simi1505/20m-SSB-TRX-Prototype-OE3SDE/Transmitter/Calculations/Buffer Amplifier/Buffer Amplifier.pdf

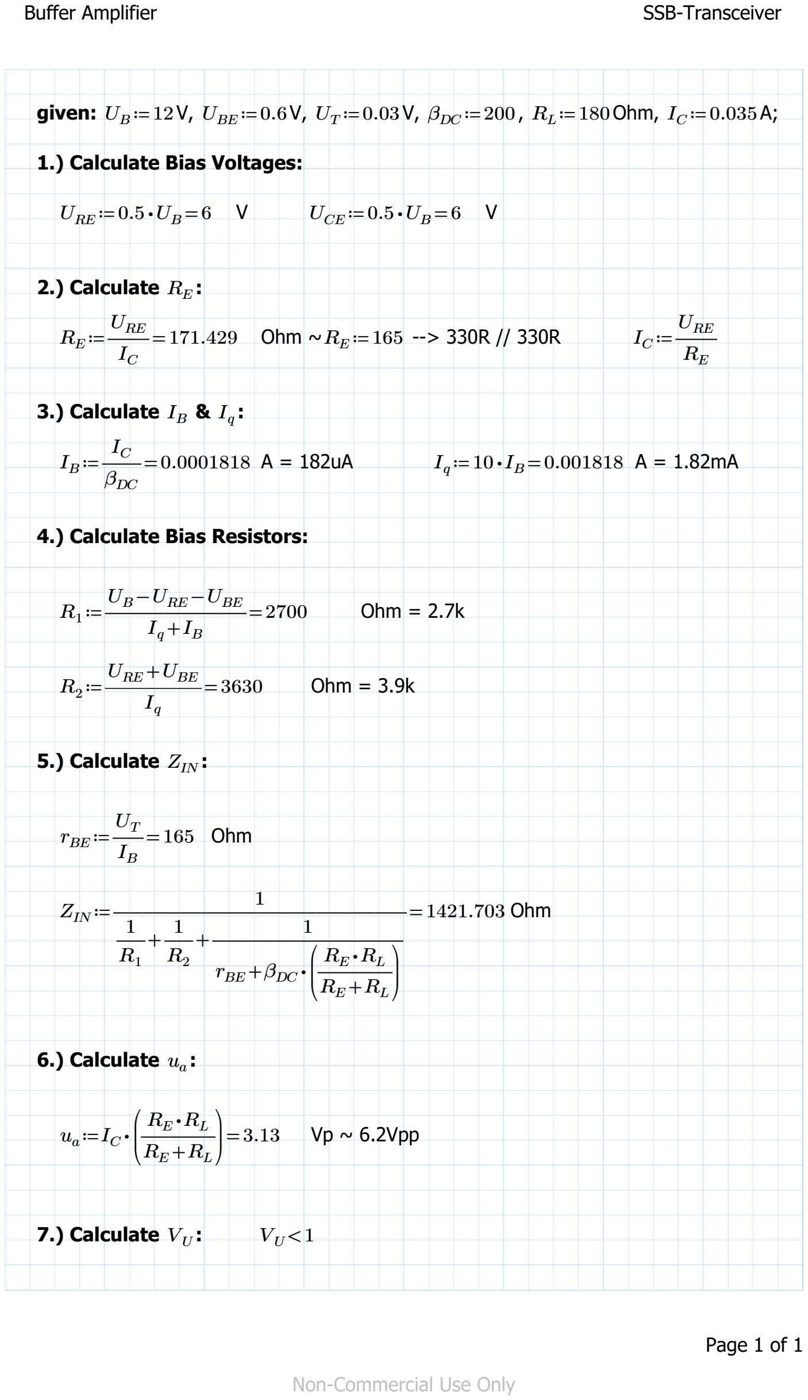
[picture p11: page 1]

Buffer Amplifier | SSB-Transceiver
given: UB≔12V, UBE≔0.6V, UT≔0.03V, βDC≔200 , R ≔ | Ohm, | A; L | 180 | IC≔0.035

1.) Calculate Bias Voltages:

URE≔0.5 ⋅UB =6 V UCE≔0.5 ⋅UB =6 V

2.) Calculate RE :

RE≔――=

URE
IC
171.429 Ohm ~RE≔165 --> 330R // 330R | IC≔――

URE
RE

3.) Calculate IB & I : q

IB≔――=

IC

βDC

0.0001818 A = 182uA | Iq≔10 ⋅ IB =0.001818 A = 1.82mA

4.) Calculate Bias Resistors:

R1≔―――――=

UB −URE −UBE
Iq+IB

2700 Ohm = 2.7k

R2≔――――=

URE +UBE
Iq

3630 Ohm = 3.9k

5.) Calculate Z : IN

rBE≔――=

UT
IB

165 Ohm

ZIN≔―――――――――――=

1

―+ +

1
R1

―1
R2

――――1 ―――

rBE +βDC ⋅

⎛
⎜
⎝

―――

RE ⋅RL
RE +RL

⎞
⎟
⎠

1421.703 Ohm

6.) Calculate u : a

ua≔IC ⋅ | =

⎛
⎜
⎝
| ―――

RE ⋅RL
RE +RL

⎞
⎟
⎠

### 3.13 Vp ~ 6.2Vpp

7.) Calculate VU : VU <1

Non-Commercial Use Only

Page 1 of 1
