simi1505/20m-SSB-TRX-Prototype-OE3SDE/Transmitter/Calculations/Driver Amplifier/Driver Amplifier.pdf

Driver Amplifier | SSB-Transceiver

geg.: UB≔12V, PO2≔1.2W, η≔0.3 , UT≔0.026V, f≔14000000Hz,
RL≔50Ohm

1.) Calculate Stage 2:

a) Calculate Voltages:

URE2≔0.1 ⋅UB =1.2V

UBE2≔0.7 V

b) Calculate bias currents: | βDC2≔180
IC2≔――⋅ | =

PO2
η ―1 ―UB
0.333 A

IB2≔――=

IC2

βDC2

0.001852 A

IQ2≔5 ⋅ IB2=0.009259 A

c) Calculate resistors:

RC2≔―――――=

⎛⎝UB −URE2⎞
⎠

2

2 ⋅PO2

### 48.6 Ohm

RE2≔――=

URE2

IC2

3.6 Ohm | RE2≔3.3 Ohm

R12≔――――――=

UB −UBE2−URE2

IB2+IQ2

909 | Ohm | R12≔1000 Ohm

R22≔――――=

UBE2+URE2

IQ2

205.2 | Ohm | R22≔220 Ohm

Non-Commercial Use Only

Page 1 of 4

d) Calculate gain resistor: | GdB2≔12 = 15.85

RE2'≔―――=

RC2

10

――

GdB2
10

3.066 Ohm

REx2≔――――=

1

――−

1

RE2'

―1―RE2

43.329 REx2≔43 Ohm

e) Calculate input resistance: | fT2≔200000000 Hz

βAC2≔――=

fT2
f

14.286 re2≔――=

UT

IC2

0.078 Ohm

RIN2≔――――――――――=

1

――+ +

1

R12

―1 ―R22

―――1 ――― βAC2 ⋅ ⎛⎝re2+RE2'⎞ ⎠

35.962 Ohm

2.) Calculate Stage 1:

a) Calculate Voltages:

URE1≔0.1 ⋅UB =1.2V

UBE1≔0.7 V

b) Calculate bias currents: | βDC1≔210

PO1≔―――=

PO2

10

――

GdB2
10

0.076 W

IC1≔――⋅ =

PO1
η ―1 ―UB
0.021 A

IB1≔――=

IC1 βDC1 | 0.0001 A

IQ1≔6 ⋅ IB1=0.000601 A

Page 2 of 4

c) Calculate resistors:

RC1≔―――――=

⎛⎝UB −URE1⎞
⎠

2

2 ⋅PO1

770.258 Ohm

RE1≔――=

URE1

IC1

57.056 Ohm | RE1≔56 Ohm

R11≔――――――=

UB −UBE1−URE1

IB1+IQ1

14406.679 Ohm R11≔15000 Ohm

R21≔――――=

UBE1+URE1

IQ1

3161.862 Ohm | R21≔3300 Ohm
d) Calculate gain resistor: | GdB1≔20 = 100

RE1'≔―――=

RC1

10

――

GdB1
10

7.703 Ohm

REx1≔――――=

1

――−

1

RE1'

―1―RE1

8.931 REx1≔8.5 Ohm

e) Calculate input resistance: | fT1≔300000000 Hz

βAC1≔――=

fT1
f

21.429 re1≔――=

UT

IC1

1.236 Ohm

RIN1≔――――――――――=

1

――+ +

1

R11

―1 ―R21

―――1 ――― βAC1 ⋅ ⎛⎝re1+RE1'⎞ ⎠

178.879 Ohm

Page 3 of 4

3.) Calculate Transformer:

a) Stage 1 output transformer:
ZP≔RC1=770.258 | Ohm | ZS≔RIN2=35.962 Ohm
| | --> Guideline: 6T:28T @ FT37-43 Toroid Core --> LP≔113.4 ⋅ 10 H @ FT37-43 Toroid Core ⁻⁶ --> LS≔5.6 ⋅ 10 H @ FT37-43 Toroid Core ⁻⁶
ü1≔ | =
―
ZP ZS | 4.628

üdB1≔10 ⋅log⎛⎝ü1

| ⎞ ⎠=6.654 dB --> 6.654dB loss!

ZP≔ZS

⋅ =

⎛
⎜

⎝―18
4

⎞
⎟
⎠

2
728.237 Ohm

Requirement:

XLP≔2 ⋅π⋅ f ⋅LP=9975.185 | Ohm > 10 ⋅RC1=7702.581 Ohm --> correct!
XLS≔2 ⋅π⋅ f ⋅LS=492.602 | Ohm > 10 ⋅R = | Ohm --> correct! IN2 359.623
b) Stage 2 output transformer:
ZP≔RC2=48.6 | Ohm | ZS≔RL=50 | Ohm

--> Guideline: 6T:28T @ FT37-43 Toroid Core
| | --> LP≔8.75 ⋅ 10 H @ FT37-43 Toroid Core ⁻⁶ --> LS≔8.75 ⋅ 10 H @ FT37-43 Toroid Core ⁻⁶
ü2≔ | =
―
ZP ZS | 0.986

üdB2≔10 ⋅log⎛⎝ü2

⎞
⎠=−0.062 dB --> 0.062dB gain!

ZP≔ZS

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
### 50 Ohm

Requirement:

XLP≔2 ⋅π⋅ f ⋅LP=769.69 | Ohm > 10 ⋅RC2=486 Ohm --> correct!
XLS≔2 ⋅π⋅ f ⋅LS=769.69 | Ohm > 10 ⋅R = | Ohm --> correct! L 500

4.) Gain of Driver Amplifier:

Gges≔GdB1−üdB1+GdB2−üdB2=25.408

Page 4 of 4
