simi1505/20m-SSB-TRX-Prototype-OE3SDE/Transmitter/Calculations/LC Double Tuned Bandpass Filter/LC Double Tuned Bandpass Filter.pdf

LC Double Tuned Bandpass Filters | SSB-Transceiver

Circuit:


1.) Define lower and upper cut off frequencies:

f1≔14000000 f2≔14400000

2.) Define inductor core, turns and value (L＝L ＝ ): 1 | L2
L≔2.12 ⋅ 10⁻⁶ | H = 2.12uH --> 23T @ T50-6 Core --> "toroids.info/T50-6.php"
QU≔240 | ... unloaded Q of the resonators

3.) Calculate ω : 0

ω0

... center angular frequency

ω0≔2 ⋅π⋅ f1

⋅f2

=89212381.366 rad/sec

4.) Calculate C : 0

C0

... nodal capacitance

C0≔―――=

1
ω ⋅ 0

### 2 L

0.0000000000593 F = 59.3pF

5.) Calculate Q : L

QL

... loaded filter Q

QL≔―――――=

ω0
2 ⋅π⋅ ⎛⎝f2−f1

⎞
⎠

35.496

Non-Commercial Use Only

Page 1 of 3

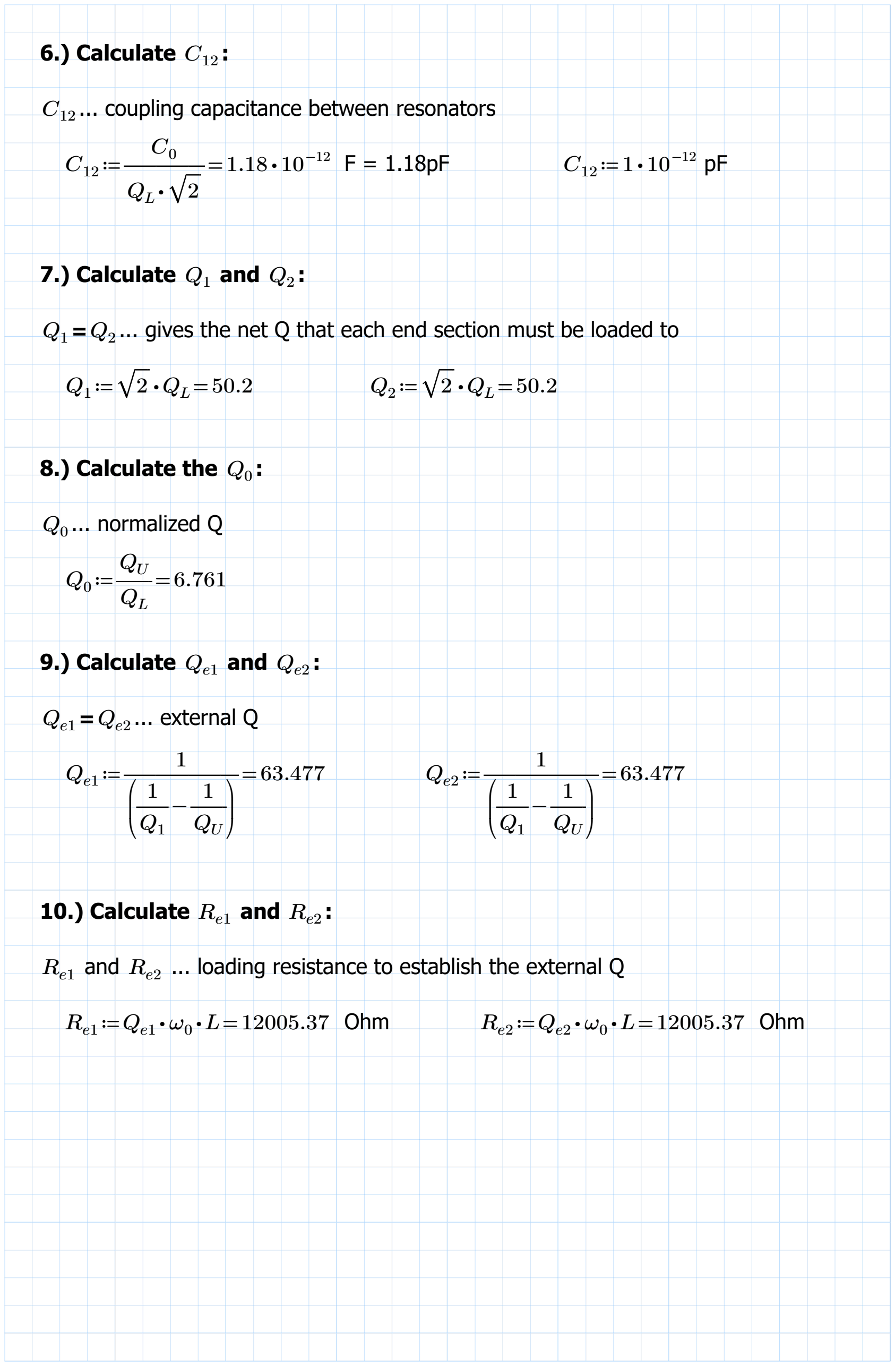
[picture p12: figure]
6.) Calculate C : 12; 7.) Calculate Q and; 8.) Calculate the Q : 0; ... normalized Q; 9.) Calculate Q and; Qe1＝Qe2 ... external Q; 10.) Calculate R and; ⋅L=12005.37 Ohm

C ... coupling capacitance between resonators 12

1.18 ⋅ 10⁻¹² F = 1.18pF | C12≔1 ⋅ 10⁻¹² pF

... gives the net Q that each end section must be loaded to

Re1 and Re2 ... loading resistance to establish the external Q

Page 2 of 3

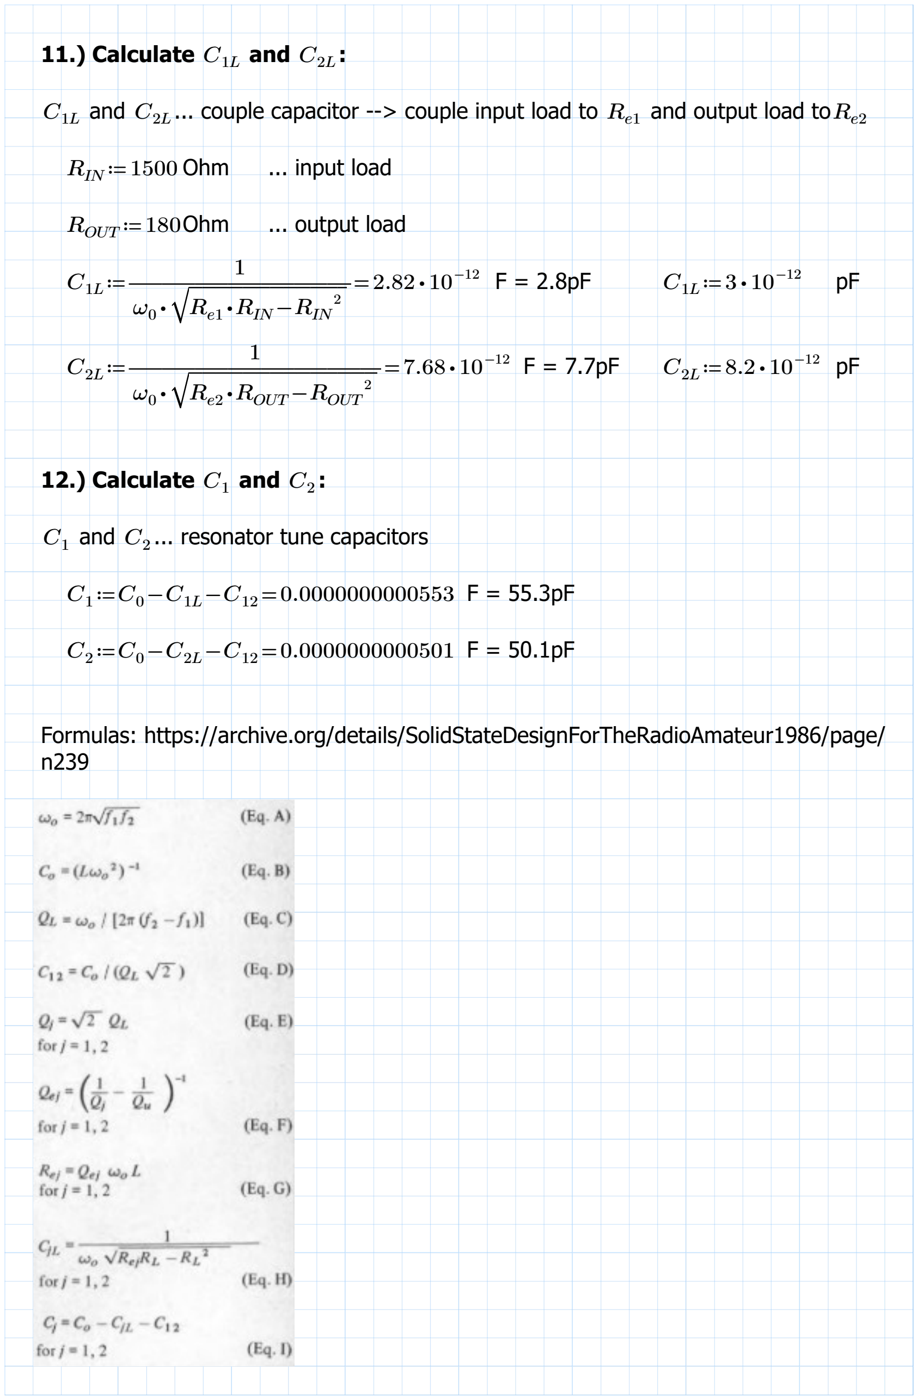
[picture p13: figure]
11.) Calculate C and; RIN≔1500 Ohm; ... input load; ROUT≔180Ohm; ... output load; − R ⋅ e1 RIN RIN; − R ⋅ e2 ROUT ROUT; 12.) Calculate C and; C and; ... resonator tune capacitors 1; Formulas: https://archive.org/details/SolidStateDesignForTheRadioAmateur1986/page/ n239

C1L and C2L ... couple capacitor --> couple input load to Re1 and output load toRe2

7.68 ⋅ 10⁻¹² F = 7.7pF C2L≔8.2 ⋅ 10⁻¹² pF

Page 3 of 3
