simi1505/20m-SSB-TRX-Prototype-OE3SDE/Transmitter/Calculations/LC Lowpass Filter/LC Lowpass Filter.pdf

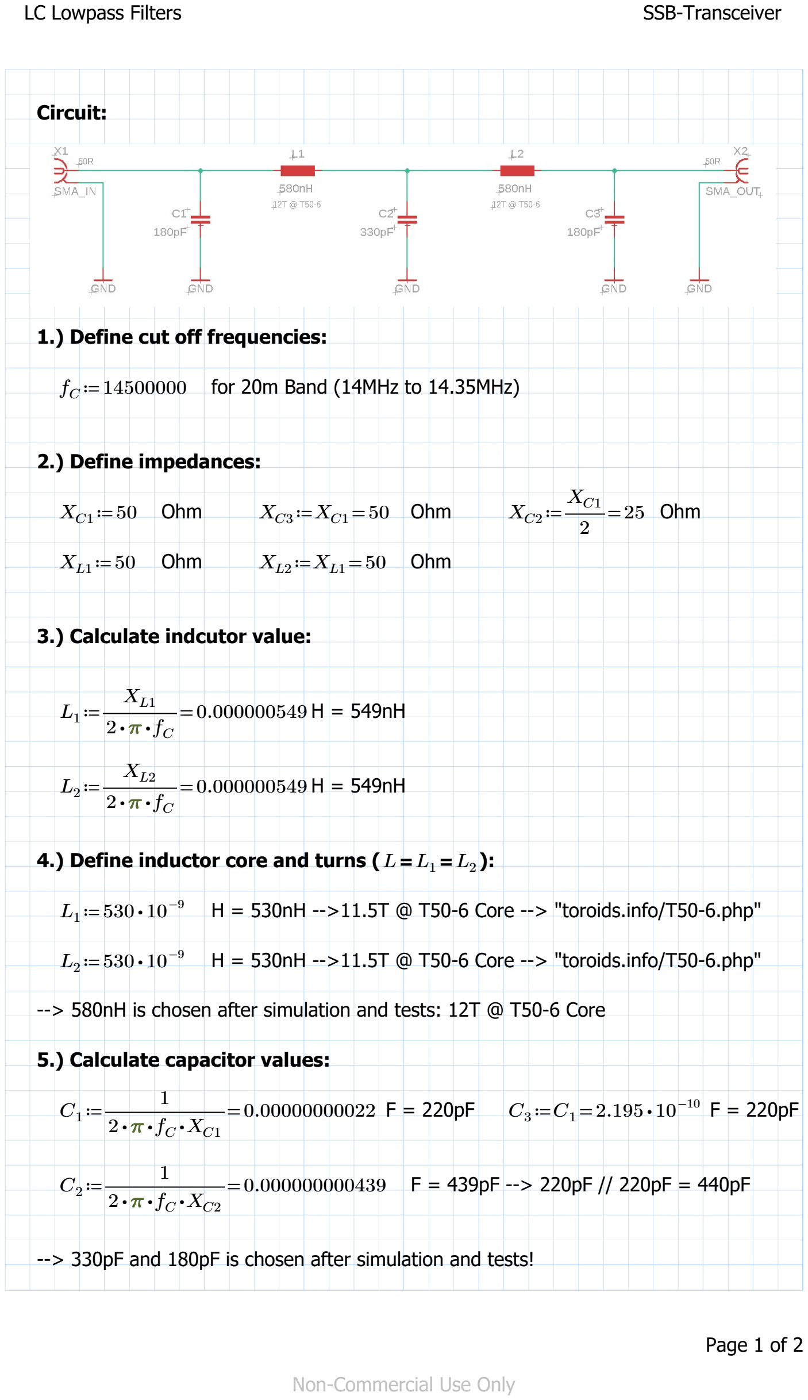
[picture p14: page 1]

LC Lowpass Filters | SSB-Transceiver

Circuit:

1.) Define cut off frequencies:

fC≔14500000 for 20m Band (14MHz to 14.35MHz)

2.) Define impedances:
XC1≔50 Ohm | XC3≔XC1=50 Ohm | XC2≔――= XC1
| | 2

### 25 Ohm

XL1≔50 Ohm XL2≔XL1=50 Ohm

3.) Calculate indcutor value:

L1≔―――=

XL1
2 ⋅π⋅ fC

0.000000549 H = 549nH

L2≔―――=

XL2
2 ⋅π⋅ fC

0.000000549 H = 549nH

4.) Define inductor core and turns (L＝L ＝ ): 1 L2

L1≔530 ⋅ 10⁻⁹ H = 530nH -->11.5T @ T50-6 Core --> "toroids.info/T50-6.php"

L2≔530 ⋅ 10⁻⁹ H = 530nH -->11.5T @ T50-6 Core --> "toroids.info/T50-6.php"

--> 580nH is chosen after simulation and tests: 12T @ T50-6 Core

5.) Calculate capacitor values:

C1≔―――――=

1 2 ⋅π⋅ fC ⋅XC1 | 0.00000000022 F = 220pF | C3≔C1=2.195 ⋅ 10⁻¹⁰ F = 220pF

C2≔―――――=

1
2 ⋅π⋅ fC ⋅XC2

0.000000000439 F = 439pF --> 220pF // 220pF = 440pF

--> 330pF and 180pF is chosen after simulation and tests!

Non-Commercial Use Only

Page 1 of 2

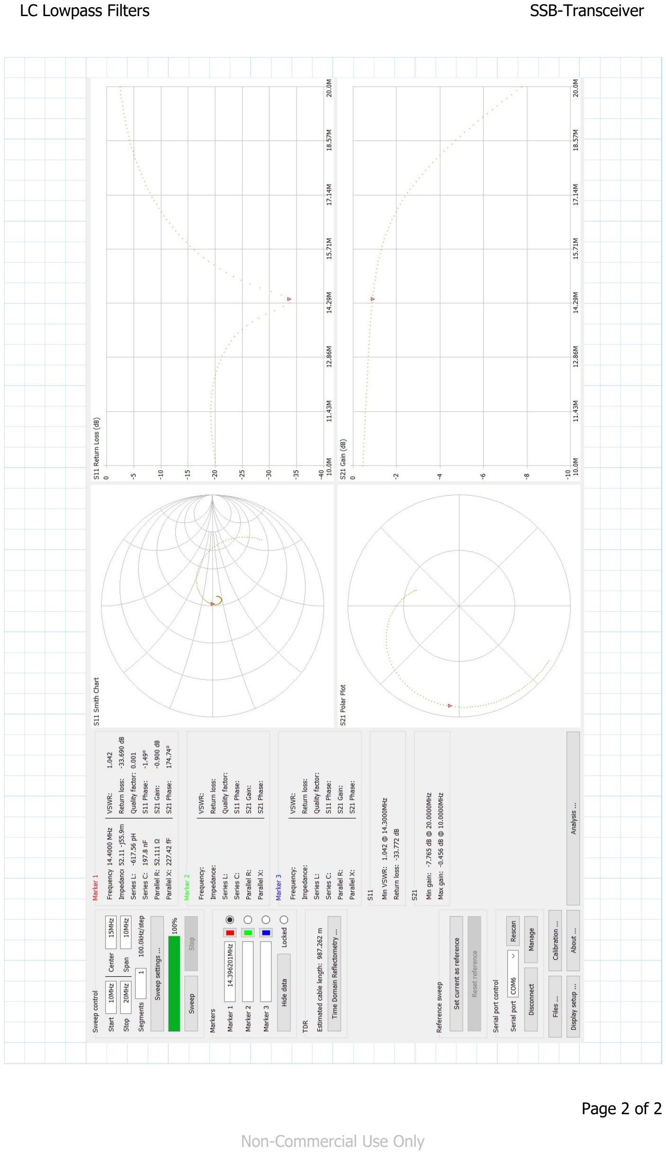
[picture p15: page 2]

LC Lowpass Filters | SSB-Transceiver

Non-Commercial Use Only

Page 2 of 2
