simi1505/20m-SSB-TRX-Prototype-OE3SDE/Transmitter/Calculations/Mic. Amplifier/Mic. Amplifier Gain.pdf

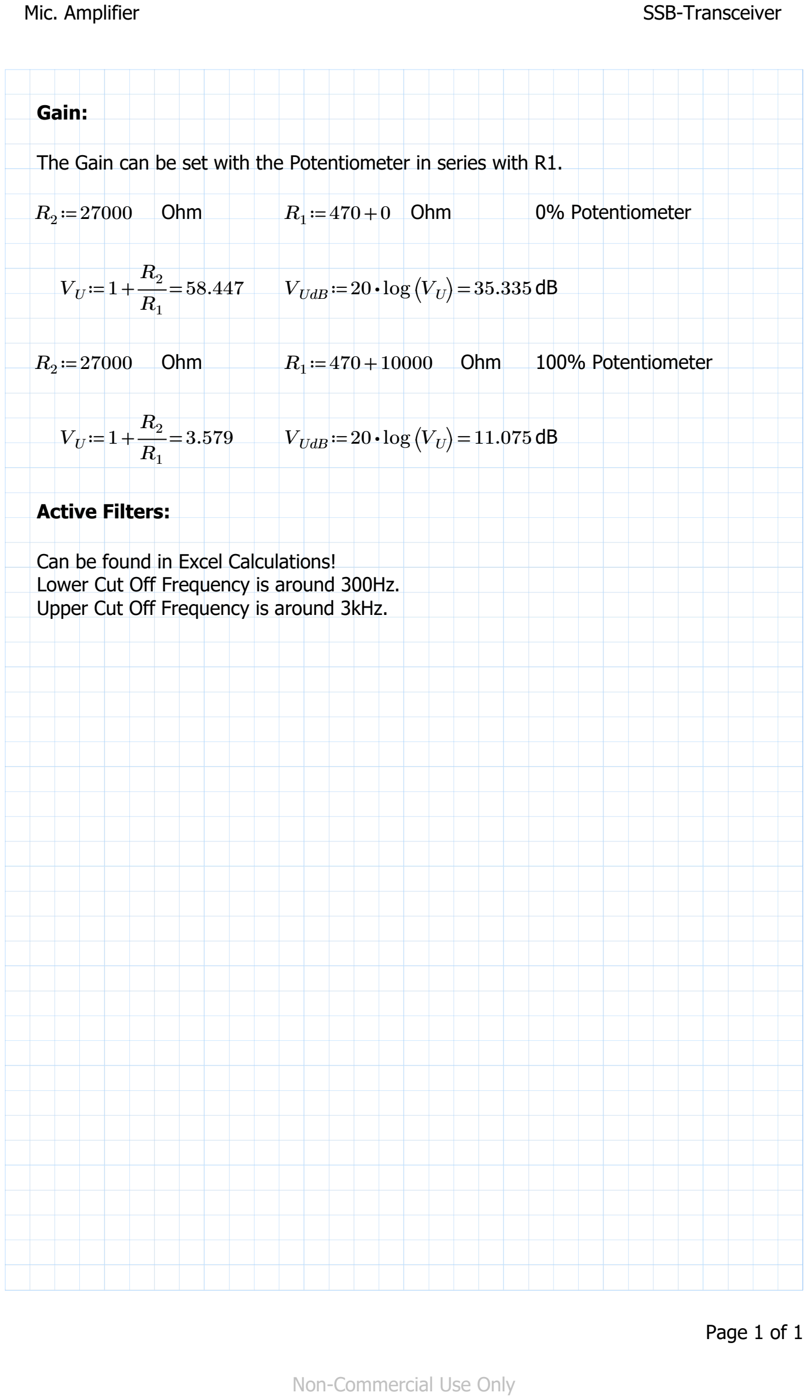
[picture p16: page 1]

Mic. Amplifier | SSB-Transceiver

Gain:

The Gain can be set with the Potentiometer in series with R1.

R2≔27000 | Ohm | R1≔470+0 Ohm | 0% Potentiometer

VU≔1+―=

| R2 R1
58.447 VUdB≔20 ⋅log⎛⎝VU
| | ⎞
⎠=35.335 dB
R2≔27000 | Ohm | R1≔470+10000 Ohm | 100% Potentiometer

VU≔1+―=

| R2 R1
3.579 VUdB≔20 ⋅log⎛⎝VU
| | ⎞
⎠=11.075 dB

Active Filters:

Can be found in Excel Calculations!
Lower Cut Off Frequency is around 300Hz. Upper Cut Off Frequency is around 3kHz.

Non-Commercial Use Only

Page 1 of 1
