simi1505/20m-SSB-TRX-Prototype-OE3SDE/Transmitter/Calculations/Power Amplifier/Power Amplifier.pdf

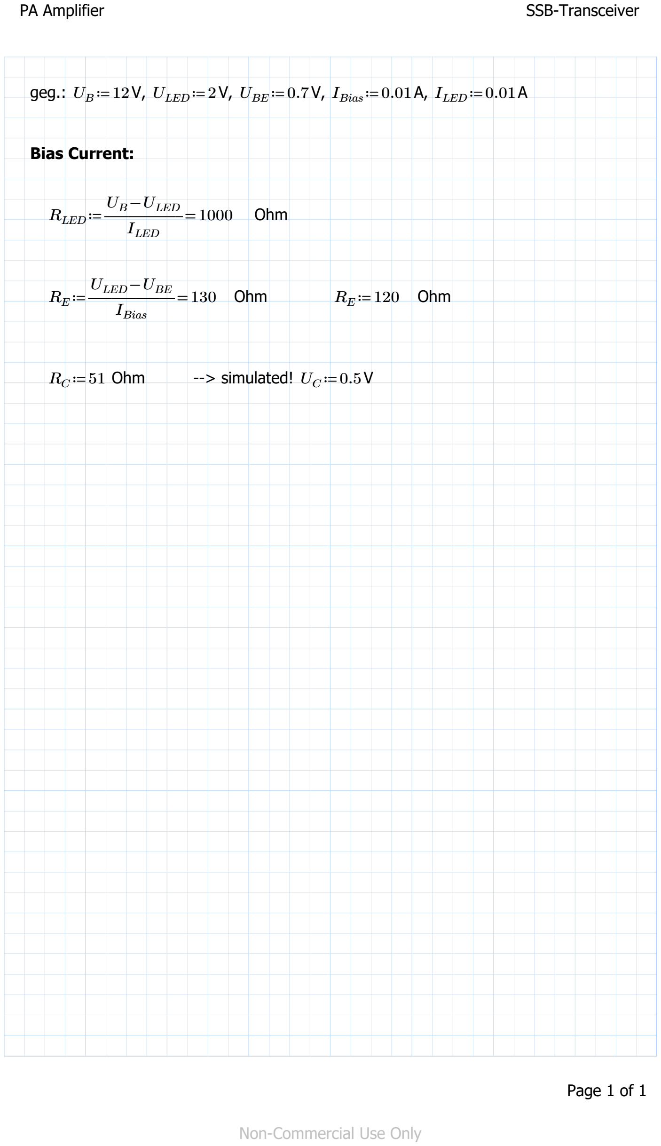
[picture p17: page 1]

PA Amplifier | SSB-Transceiver

geg.: UB≔12V, ULED≔2V, UBE≔0.7V, IBias≔0.01A, ILED≔0.01A

Bias Current:

RLED≔――――=

UB −ULED

ILED

1000 Ohm

RE≔――――=

ULED −UBE

IBias

130 Ohm | RE≔120 Ohm
RC≔51 Ohm | --> simulated! UC≔0.5V

Non-Commercial Use Only

Page 1 of 1
