simi1505/20m-SSB-TRX-Prototype-OE3SDE/Receiver/Eagle Files/LC Double Tuned Bandpass Filters/SSB Transceiver_LC Double Tuned Bandpass Filter_Circuit.pdf

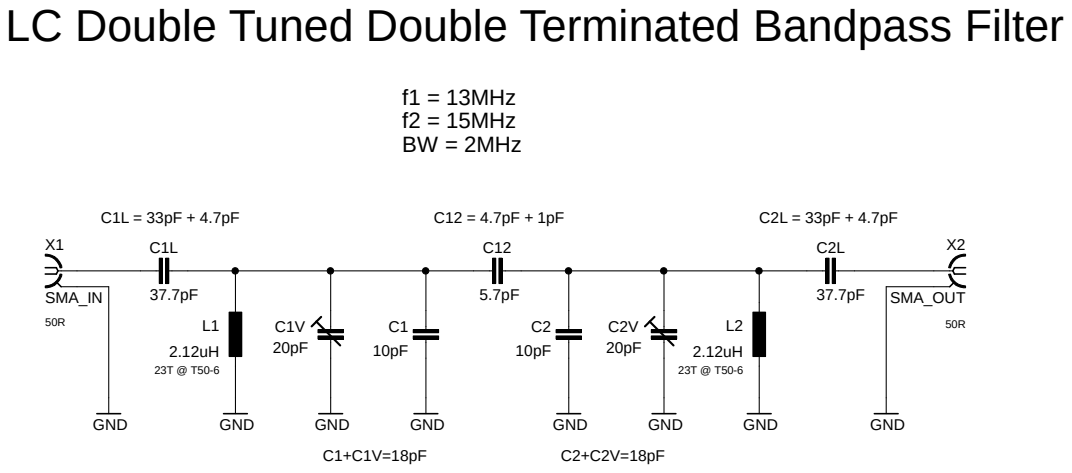
[picture p25: page 1]

11/02/2020 19:53 E:\Simon Dorrer\DIY Projekte\Amateurfunkprojekte\SSB Transceiver\Receiver\Eagle Files\LC Double Tuned Bandpass Filters\SSB Transceiver_LC Double Tuned Bandpass Filter.sch (Sheet: 1/1) 50R 50R C1+C1V=18pF C2+C2V=18pF 23T @ T50-6 23T @ T50-6 f1 = 13MHz f2 = 15MHz BW = 2MHz LC Double Tuned Double Terminated Bandpass Filter C1L = 33pF + 4.7pF C2L = 33pF + 4.7pF C12 = 4.7pF + 1pF SMA_IN SMA_OUT GND GND 37.7pF 5.7pF 10pF 10pF 37.7pF GND GND GND GND 2.12uH 2.12uH 20pF 20pF GND GND X1 C1L C12 X2 C1 C2 C2L L1 L2 C1V C2V Date: Sheet: REV: TITLE: Document Number: 11/02/2020 19:50 1/1 SSB Transceiver_LC Double Tuned Bandpass Filter
