simi1505/20m-SSB-TRX-Prototype-OE3SDE/Receiver/Eagle Files/MC1496 Product Detector/SSB Transceiver_MC1496 Product Detector_Circuit.pdf

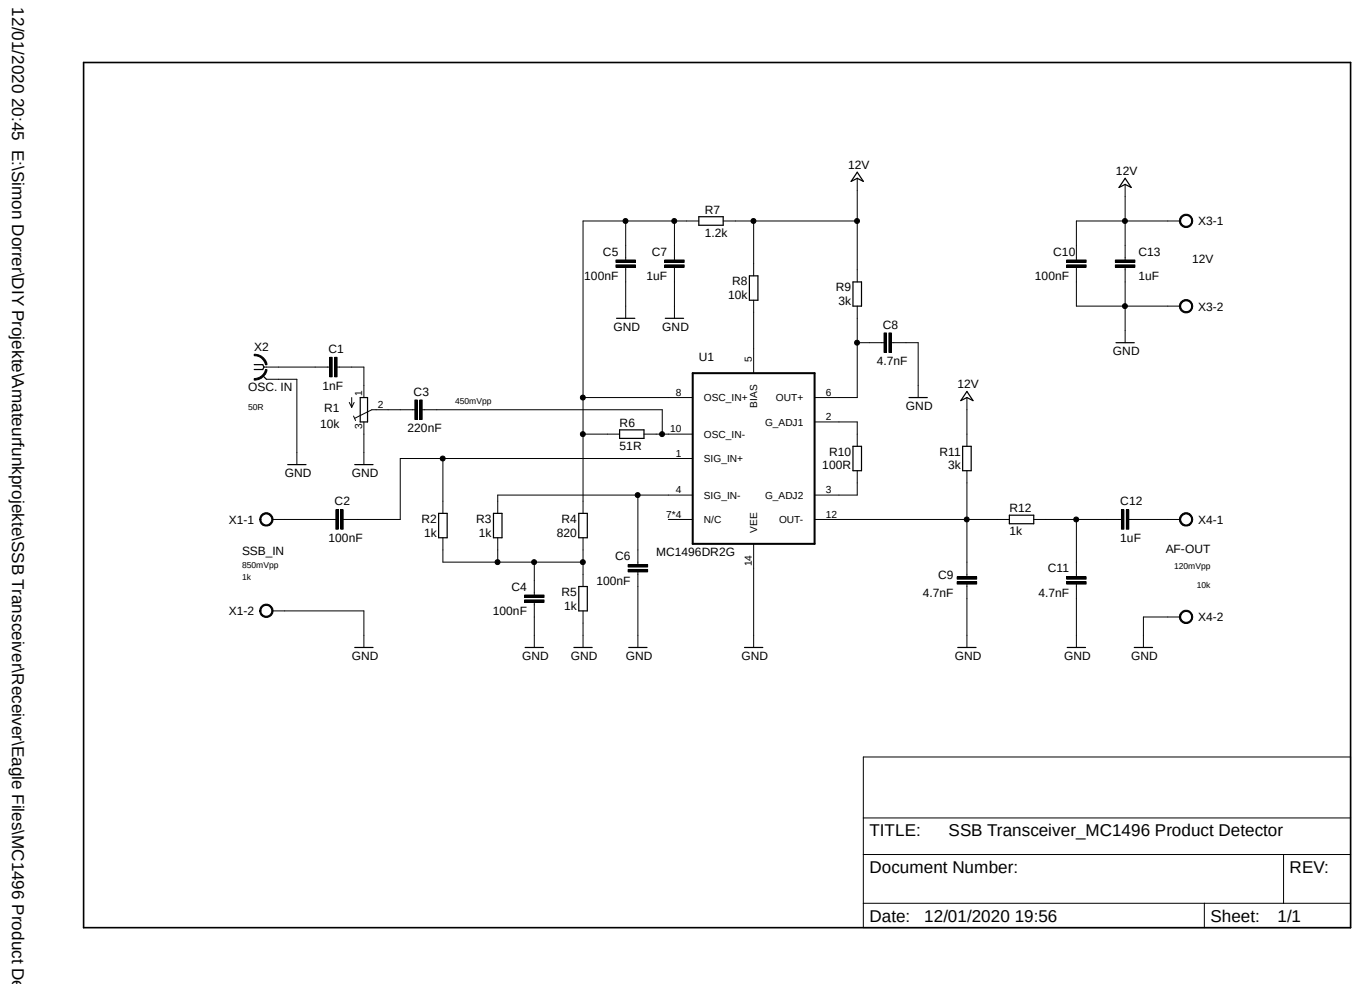
[picture p26: page 1]

12/01/2020 20:45 E:\Simon Dorrer\DIY Projekte\Amateurfunkprojekte\SSB Transceiver\Receiver\Eagle Files\MC1496 Product Detector\SSB Transceiver_MC1496 Product Detector.sch (Sheet: 1/1) 10k 120mVpp 50R 450mVpp 850mVpp 1k GND 12V GND OSC. IN 1nF 10k 220nF GND 51R 1k MC1496DR2G 1uF 100R SSB_INGND 1uF 12V GND 10k 1.2k 100nF 1uF 8201k 1k 100nF GND GND 100nFGND GND GND 100nF 3k 4.7nFGND AF-OUT 4.7nF 4.7nF 1k 3k12V GND GND 12V 100nFGND X3-1 X3-2 X2 C1

14 OUT- 12 U1 C12 R10 X1-1 X1-2 C13 R8 R7 C5 C7 R4 R5 R2 C6 C2 C10 R9 C8 X4-1 X4-2 C11 C9 R12 R11 C4 Date: Sheet: REV: TITLE: Document Number: 12/01/2020 19:56 1/1 SSB Transceiver_MC1496 Product Detector
