simi1505/20m-SSB-TRX-Prototype-OE3SDE/Receiver/Eagle Files/SA612 Mixer/SSB Transceiver_SA612 Mixer_Circuit.pdf

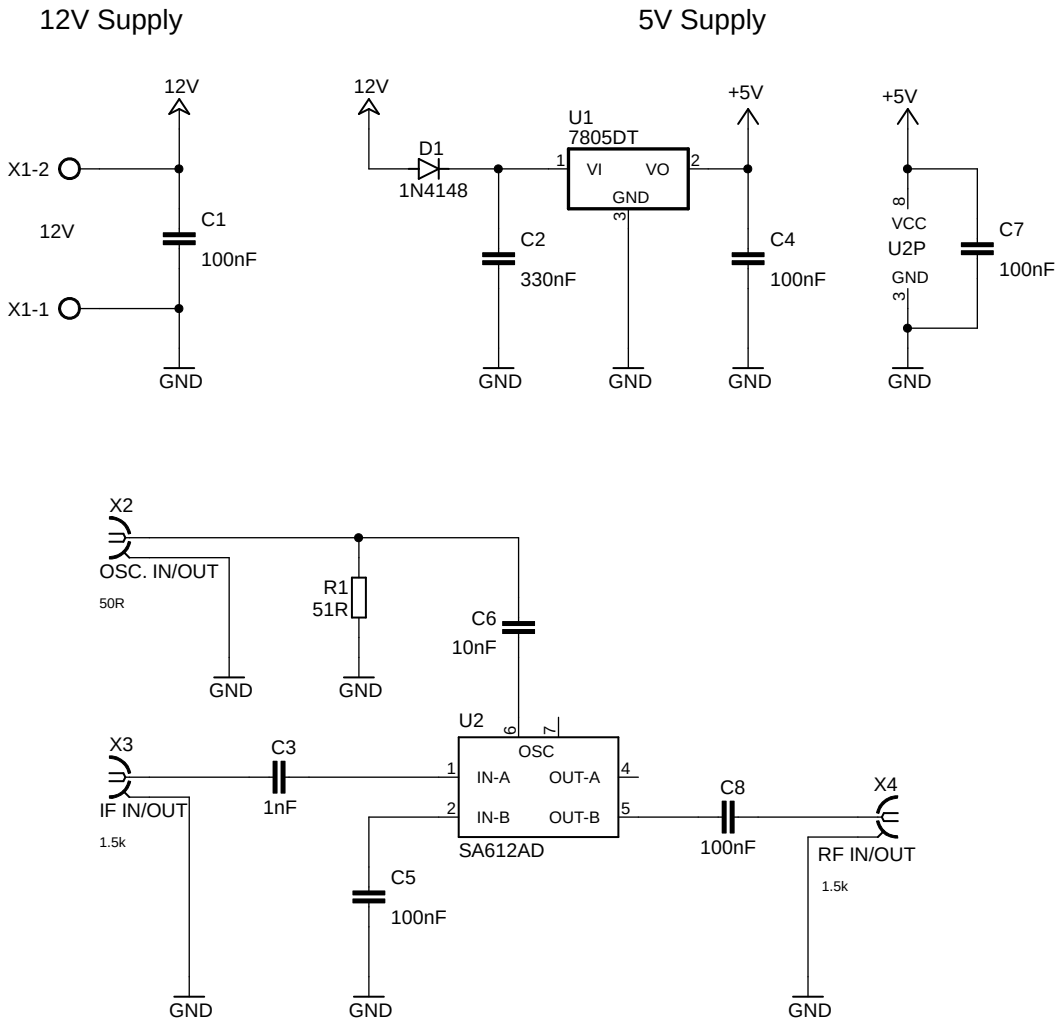
[picture p27: page 1]

12/01/2020 17:15 E:\Simon Dorrer\DIY Projekte\Amateurfunkprojekte\SSB Transceiver\Transmitter\Eagle Files\SA612 Mixer\SSB Transceiver_SA612 Mixer.sch (Sheet: 1/1) 1.5k 50R 1.5k 12V Supply 5V Supply RF IN/OUT GND OSC. IN/OUTGND 100nF 12V GND IF IN/OUT 12V +5V 7805DT 330nF 100nF 1N4148SA612AD 100nF GND 1nF 10nF 100nF GND GND GND GND GND +5V 100nF 12V 51RGND X4 X2 C1 X3 X1-1 X1-2 GND VI 1

8 3 U2P C5 C3 C6 C8 C7 R1 Date: Sheet: REV: TITLE: Document Number: 12/01/2020 17:14 1/1 SSB Transceiver_SA612 Mixer
