simi1505/20m-SSB-TRX-Prototype-OE3SDE/Receiver/Eagle Files/Speaker Amplifier/SSB Transceiver_Speaker Amplifier_Circuit.pdf

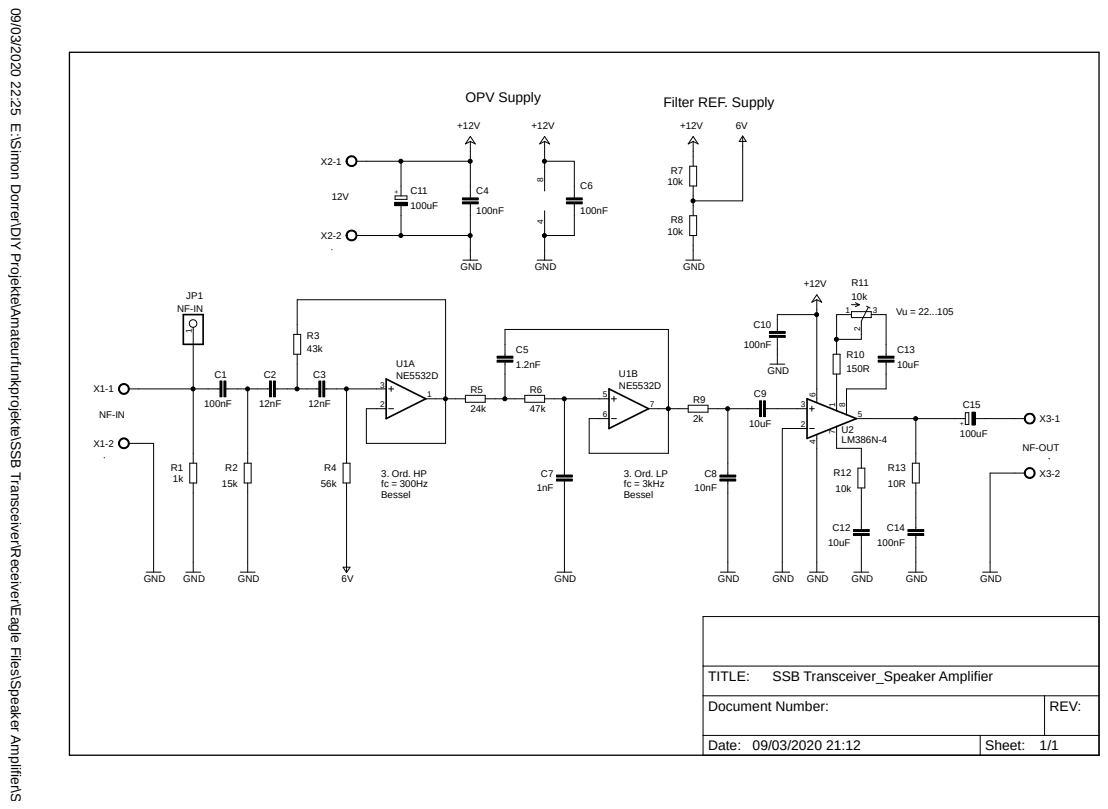
[picture p28: page 1]

09/03/2020 22:25 E:\Simon Dorrer\DIY Projekte\Amateurfunkprojekte\SSB Transceiver\Receiver\Eagle Files\Speaker Amplifier\SSB Transceiver_Speaker Amplifier.sch (Sheet: 1/1) OPV Supply Filter REF. Supply 3. Ord. HP fc = 300Hz Bessel 3. Ord. LP fc = 3kHz Bessel NF-IN Vu = 22...105 1kGND GND +12V 12V +12V GND100nF NF-IN NF-OUT GND 10k+12V 10kGND 6V 100nF 100nF15kGND GND 12nF 12nF 43k56k 6V 24k 47k 1.2nF1nFGND 2k10nFGND 10uFGND GND10uF 10k NE5532D NE5532D GND +12V 100nFGND 10R 100nFGND 10uF 150R 10k 100uF 100uF LM386N-4

7U2 Date: Sheet: REV: TITLE: Document Number: 09/03/2020 21:12 1/1 SSB Transceiver_Speaker Amplifier
