simi1505/20m-SSB-TRX-Prototype-OE3SDE/Receiver/Eagle Files/Supply EMI Filter/SSB Transceiver_Supply EMI Filter_Circuit.pdf

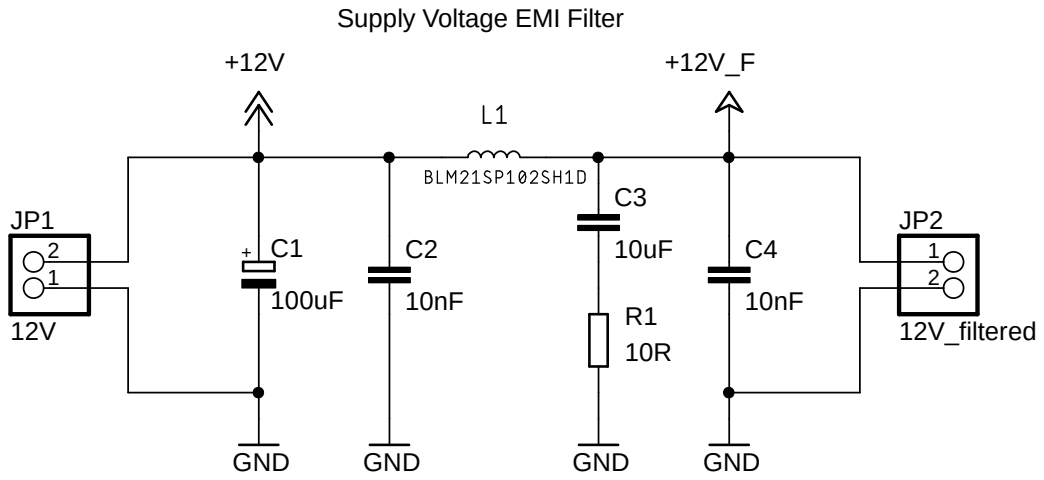
[picture p29: page 1]
Date:; Sheet:; REV: TITLE: Document Number: 07/01/2020 20:35; 1/1 SSB Transceiver_Supply EMI Filter

07/01/2020 20:36 E:\Simon Dorrer\DIY Projekte\Amateurfunkprojekte\SSB Transceiver\Transmitter\Eagle Files\Supply EMI Filter\SSB Transceiver_Supply EMI Filter.sch (Sheet: 1/1) Supply Voltage EMI Filter +12V100uF 10nF 10uF 10nF 10R+12V_F GND GND GND GND 12V 12V_filtered C1 C2 C3 C4 R1
