simi1505/20m-SSB-TRX-Prototype-OE3SDE/Transmitter/Eagle Files/Buffer Amplifier/SSB Transceiver_Buffer Amplifier_Circuit.pdf

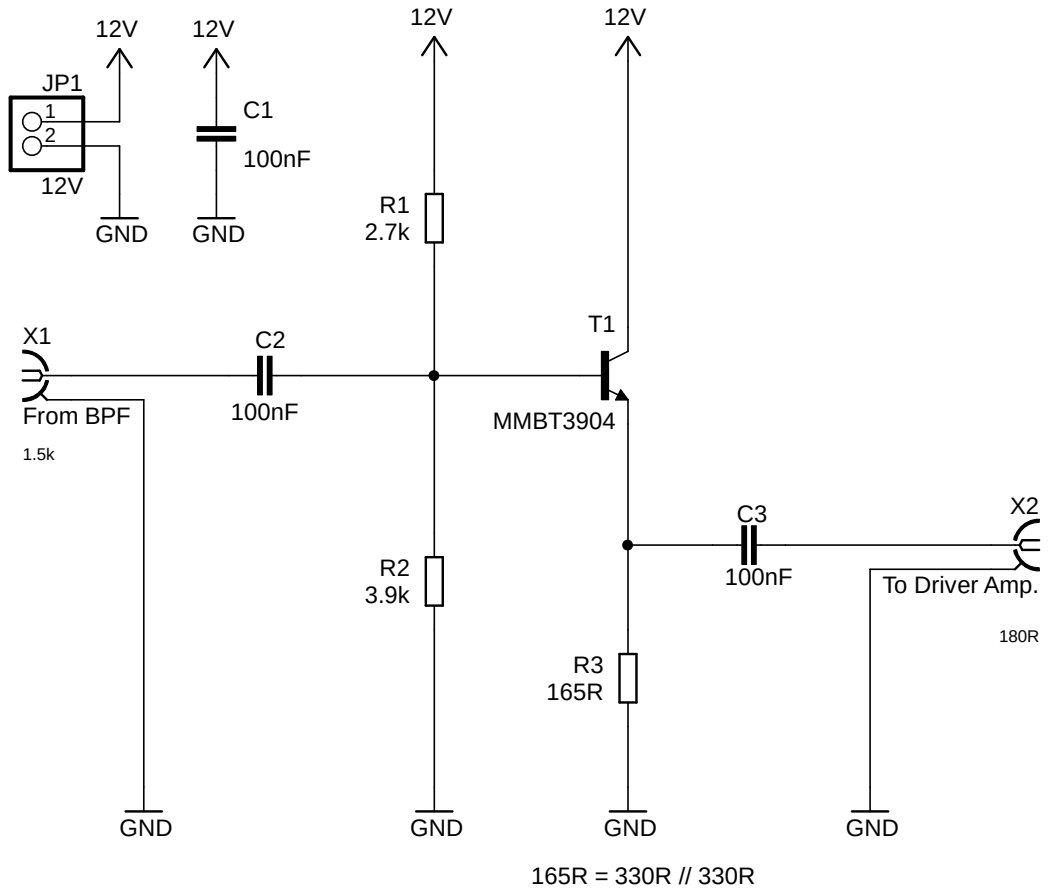
[picture p30: page 1]
Date:; Sheet:; REV: TITLE: Document Number: 01/05/2020 19:50; 1/1 SSB Transceiver_Buffer Amplifier

01/05/2020 19:50 E:\Simon Dorrer\DIY Projekte\Amateurfunkprojekte\SSB Transceiver\Transmitter\Eagle Files\Buffer Amplifier\SSB Transceiver_Buffer Amplifier.sch (Sheet: 1/1) 1.5k 180R 165R = 330R // 330R From BPF To Driver Amp. 100nF 100nF 2.7k 3.9k 165R12V MMBT3904 GND GND 12V GND 12V 12V GND100nF GND 12VGND X1 X2 C2 C3 R1 R2 R3T1
