simi1505/20m-SSB-TRX-Prototype-OE3SDE/Transmitter/Eagle Files/Crystal Ladder Filter/SSB Transceiver_Crystal Ladder Filter_Circuit.pdf

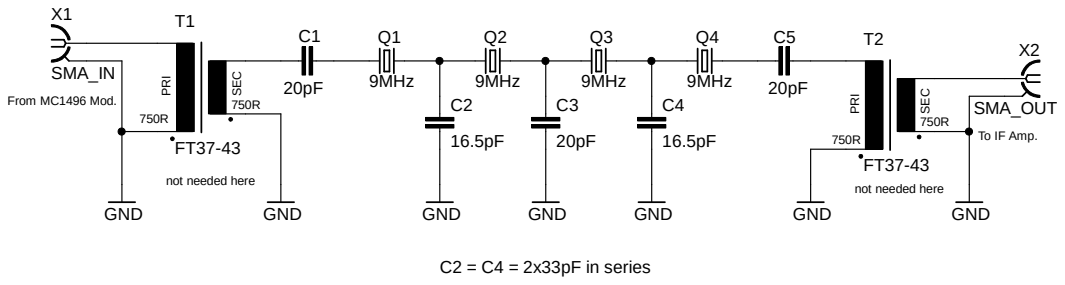
[picture p31: page 1]

13/01/2020 09:25 E:\Simon Dorrer\DIY Projekte\Amateurfunkprojekte\SSB Transceiver\Transmitter\Eagle Files\Crystal Ladder Filter\SSB Transceiver_Crystal Ladder Filter.sch (Sheet: 1/1) not needed here 750R 750R 750R 750R C2 = C4 = 2x33pF in series From MC1496 Mod. To IF Amp. not needed here SMA_OUT 9MHz 9MHz 9MHz 9MHz 20pF 16.5pF 20pF 16.5pF 20pF GND GND GND SMA_INGND GND FT37-43 FT37-43 GND GND X2 C1 Q1 Q2 Q3 Q4 C2 C3 C4 C5 X1 T1 T2 Date: Sheet: REV: TITLE: Document Number: 13/01/2020 09:25 1/1 SSB Transceiver_Crystal Ladder Filter
