simi1505/20m-SSB-TRX-Prototype-OE3SDE/Transmitter/Eagle Files/Driver Amplifier/SSB Transceiver_Driver Amplifier_Circuit.pdf

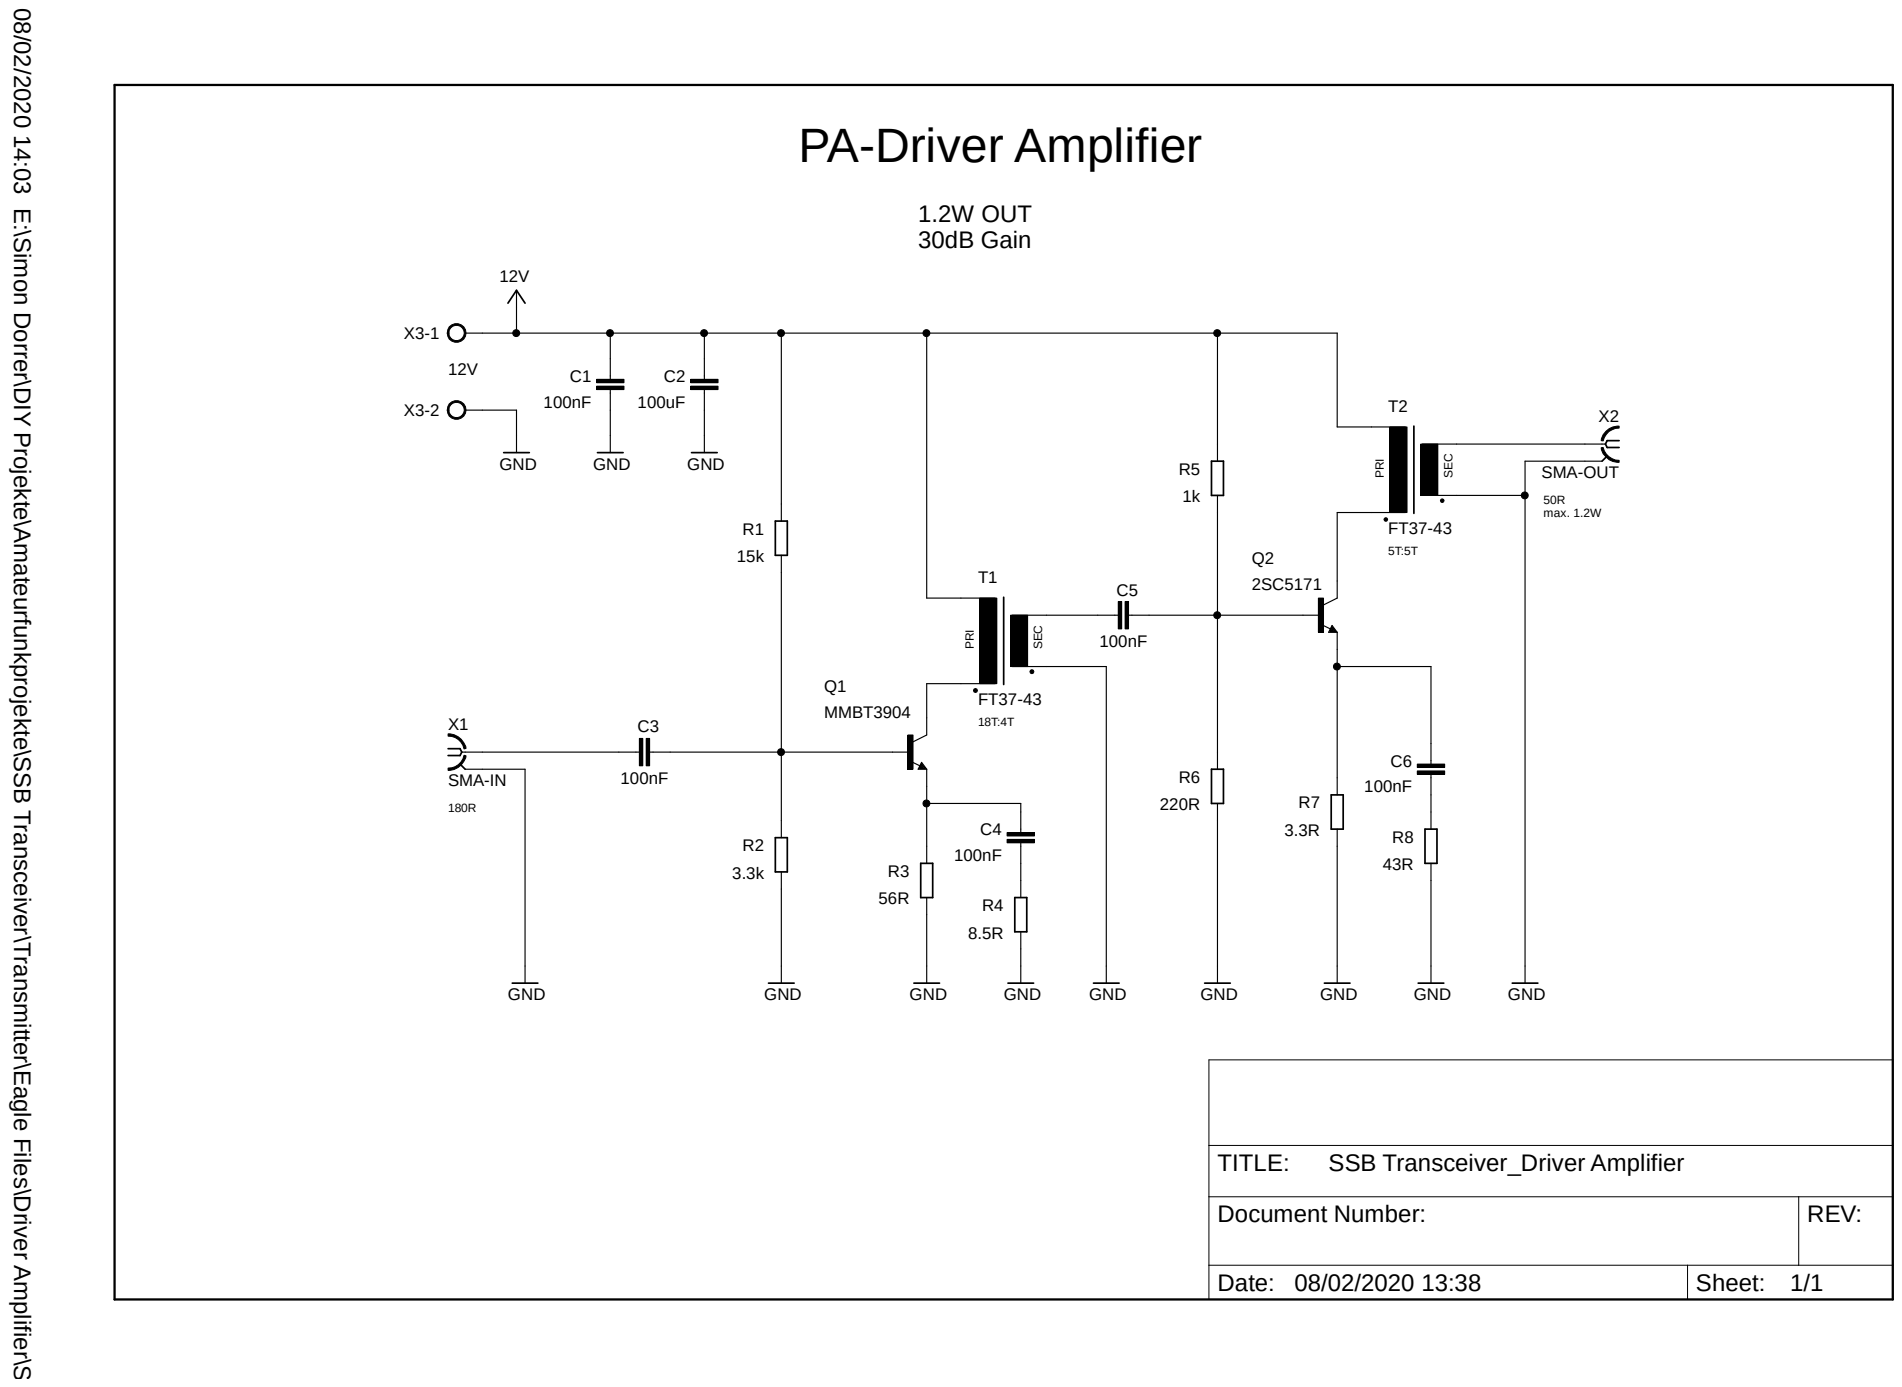
[picture p32: page 1]

08/02/2020 14:03 E:\Simon Dorrer\DIY Projekte\Amateurfunkprojekte\SSB Transceiver\Transmitter\Eagle Files\Driver Amplifier\SSB Transceiver_Driver Amplifier.sch (Sheet: 1/1) 50R max. 1.2W 180R PA-Driver Amplifier 1.2W OUT 30dB Gain 5T:5T 18T:4T 2SC5171 MMBT3904 FT37-43 FT37-43 SMA-IN SMA-OUT 100nF 100uF 100nF 100nF 100nF 100nF 15k 3.3k 56R 8.5R 1k 220R 3.3R 43R 12V GND 12VGND GND GND GND GND GND GND GND GND GND GND Q2 Q1 T1 T2 X1 X2 C1 C2 C3 C4 C5 C6 R1 R2 R3 R4 R5 R6 R7 R8 X3-1 X3-2 Date: Sheet: REV: TITLE: Document Number: 08/02/2020 13:38 1/1 SSB Transceiver_Driver Amplifier
