simi1505/20m-SSB-TRX-Prototype-OE3SDE/Transmitter/Eagle Files/LC Double Tuned Bandpass Filters/SSB Transceiver_LC Double Tuned Bandpass Filter_Circuit.pdf

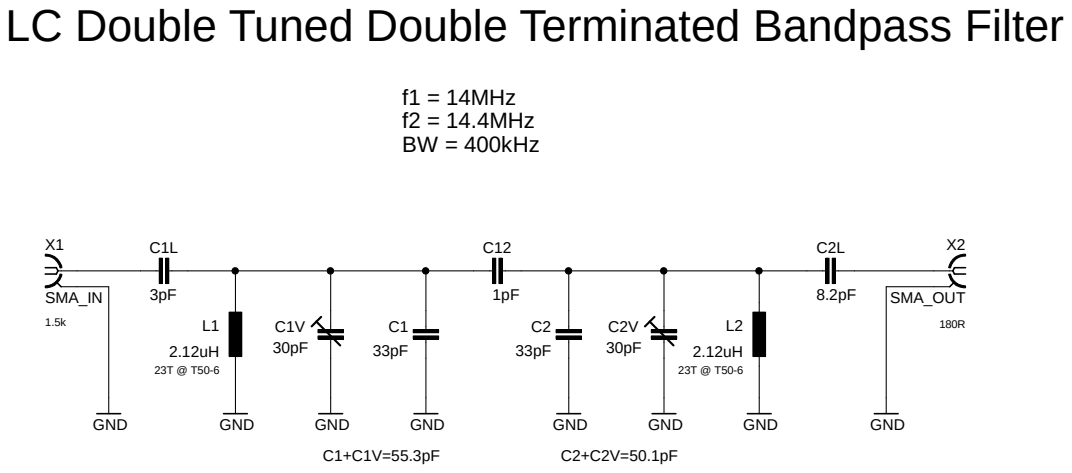
[picture p33: page 1]

08/02/2020 17:09 E:\Simon Dorrer\DIY Projekte\Amateurfunkprojekte\SSB Transceiver\Transmitter\Eagle Files\LC Double Tuned Bandpass Filters\SSB Transceiver_LC Double Tuned Bandpass Filter.sch (Sheet: 1/1) 1.5k 180R C1+C1V=55.3pF C2+C2V=50.1pF 23T @ T50-6 23T @ T50-6 f1 = 14MHz f2 = 14.4MHz BW = 400kHz LC Double Tuned Double Terminated Bandpass Filter SMA_IN SMA_OUT GND GND 3pF 1pF 33pF 33pF 8.2pF GND GND GND GND 2.12uH 2.12uH 30pF 30pF GND GND X1 C1L C12 X2 C1 C2 C2L L1 L2 C1V C2V Date: Sheet: REV: TITLE: Document Number: 08/02/2020 17:06 1/1 SSB Transceiver_LC Double Tuned Bandpass Filter
