simi1505/20m-SSB-TRX-Prototype-OE3SDE/Transmitter/Eagle Files/LC Lowpass Filter/SSB Transceiver_LC Lowpass Filter_Circuit.pdf

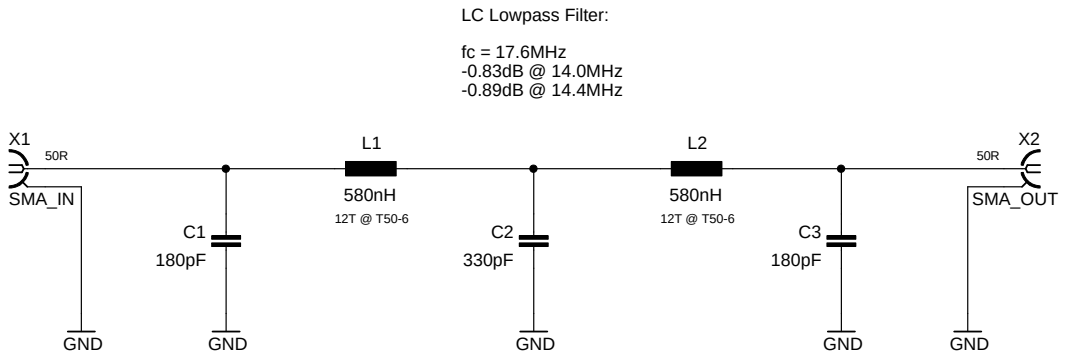
[picture p34: page 1]

29/01/2020 12:11 E:\Simon Dorrer\DIY Projekte\Amateurfunkprojekte\SSB Transceiver\Transmitter\Eagle Files\LC Lowpass Filter\SSB Transceiver_LC Lowpass Filter.sch (Sheet: 1/1) 50R 50R LC Lowpass Filter: fc = 17.6MHz -0.83dB @ 14.0MHz -0.89dB @ 14.4MHz 12T @ T50-6 12T @ T50-6 SMA_IN SMA_OUT GND GND 580nH 180pF 330pF 580nH 180pF GND GND GND X1 L1 X2 C1 C2 L2 C3 Date: Sheet: REV: TITLE: Document Number: 29/01/2020 12:07 1/1 SSB Transceiver_LC Lowpass Filter
