simi1505/20m-SSB-TRX-Prototype-OE3SDE/Transmitter/Eagle Files/MC1496 DSB Modulator/SSB Transceiver_MC1496 DSB Modulator_Circuit.pdf

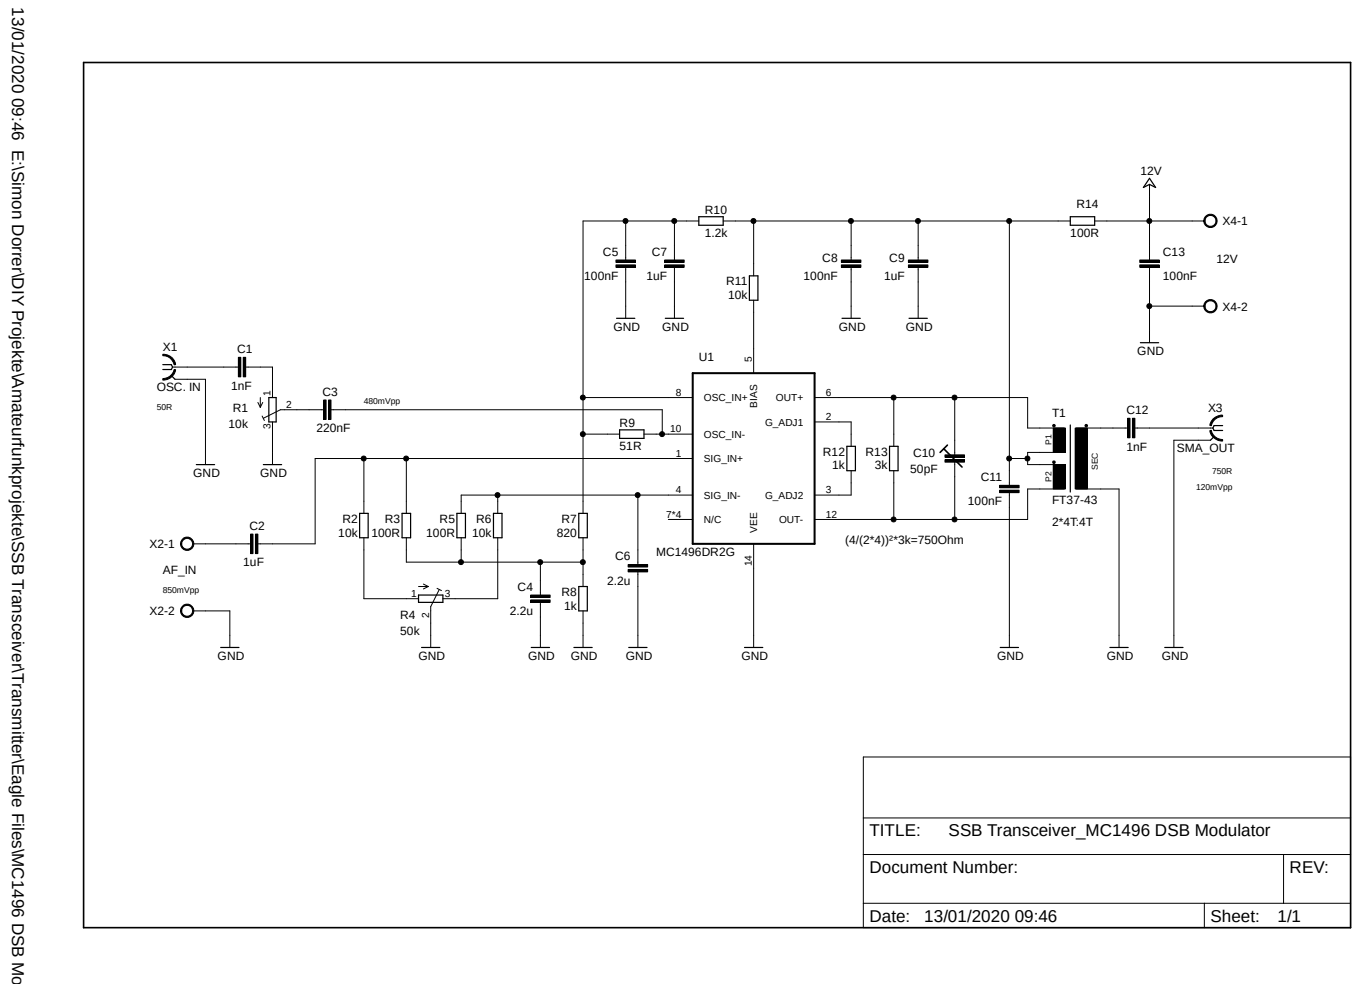
[picture p35: page 1]

13/01/2020 09:46 E:\Simon Dorrer\DIY Projekte\Amateurfunkprojekte\SSB Transceiver\Transmitter\Eagle Files\MC1496 DSB Modulator\SSB Transceiver_MC1496 DSB Modulator.sch (Sheet: 1/1) 750R 120mVpp 50R 480mVpp 850mVpp (4/(2*4))²*3k=750Ohm 2*4T:4T SMA_OUT GND 12V GND OSC. IN 1nF 10k 220nF GND 51R 10k MC1496DR2G 1nF GND 1k AF_IN 100nFGND 50k GND 3k 50pF 100nF 12V GND 100R 10k 1.2k 100nF 1uF 1uF 100nF 8201k 10k GND 2.2uGND 100R 100R GND 2.2uGND 1uF GND GND GND GND GND FT37-43 X3X4-1 X4-2 X1 C1

14 OUT- 12 U1 C12 R12 X2-1 X2-2 C11 1 3 R4 2 R13 C10 C13 R14 R11 R10 C5 C7 C8 C9 R7 R8 R2 C6 R3 R5 C4 C2 T1 Date: Sheet: REV: TITLE: Document Number: 13/01/2020 09:46 1/1 SSB Transceiver_MC1496 DSB Modulator
