simi1505/20m-SSB-TRX-Prototype-OE3SDE/Transmitter/Eagle Files/Mic. Amplifier/SSB Transceiver_Mic. Amplifier_Circuit.pdf

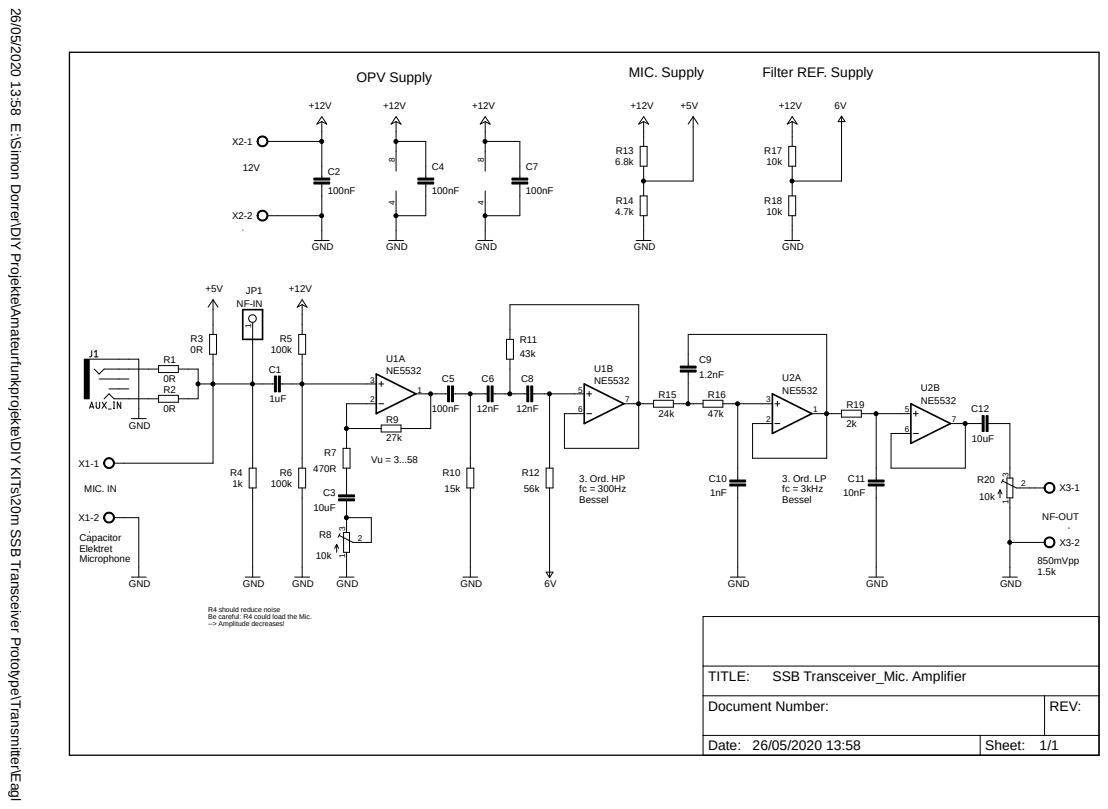
[picture p36: page 1]

26/05/2020 13:58 E:\Simon Dorrer\DIY Projekte\Amateurfunkprojekte\DIY KITs\20m SSB Transceiver Prototype\Transmitter\Eagle Files\Mic. Amplifier\SSB Transceiver_Mic. Amplifier.sch (Sheet: 1/1) Capacitor Elektret Microphone OPV Supply MIC. Supply Filter REF. Supply Vu = 3...58 3. Ord. HP fc = 300Hz Bessel 3. Ord. LP fc = 3kHz Bessel 850mVpp 1.5k R4 should reduce noise Be careful: R4 could load the Mic. --> Amplitude decreases! GND 0R0R NF-IN 1k 100k NE5532 NE5532 GND 1uF 100k+12V GND470R 27k GND GND +12V 12V +12V GND100nF 6.8k+12V 4.7kGND 0R MIC. IN NF-OUT GND 10k+12V 10kGND +5V +5V 6V NE5532 NE5532 10uF 10k 10k 100nF 100nF +12V GND 10uF 100nF 15kGND GND 12nF 12nF 43k 56k 6V 24k 47k 1.2nF 1nFGND 2k 10nFGND R1 R2

8 4 C4 C7 C3 C5R10 C6 C8 R11 R12 R15 R16 C9C10 R19 C11 Date: Sheet: REV: TITLE: Document Number: 26/05/2020 13:58 1/1 SSB Transceiver_Mic. Amplifier
