simi1505/20m-SSB-TRX-Prototype-OE3SDE/Transmitter/Eagle Files/Power Amplifier/SSB Transceiver_Power Amplifier_Circuit.pdf

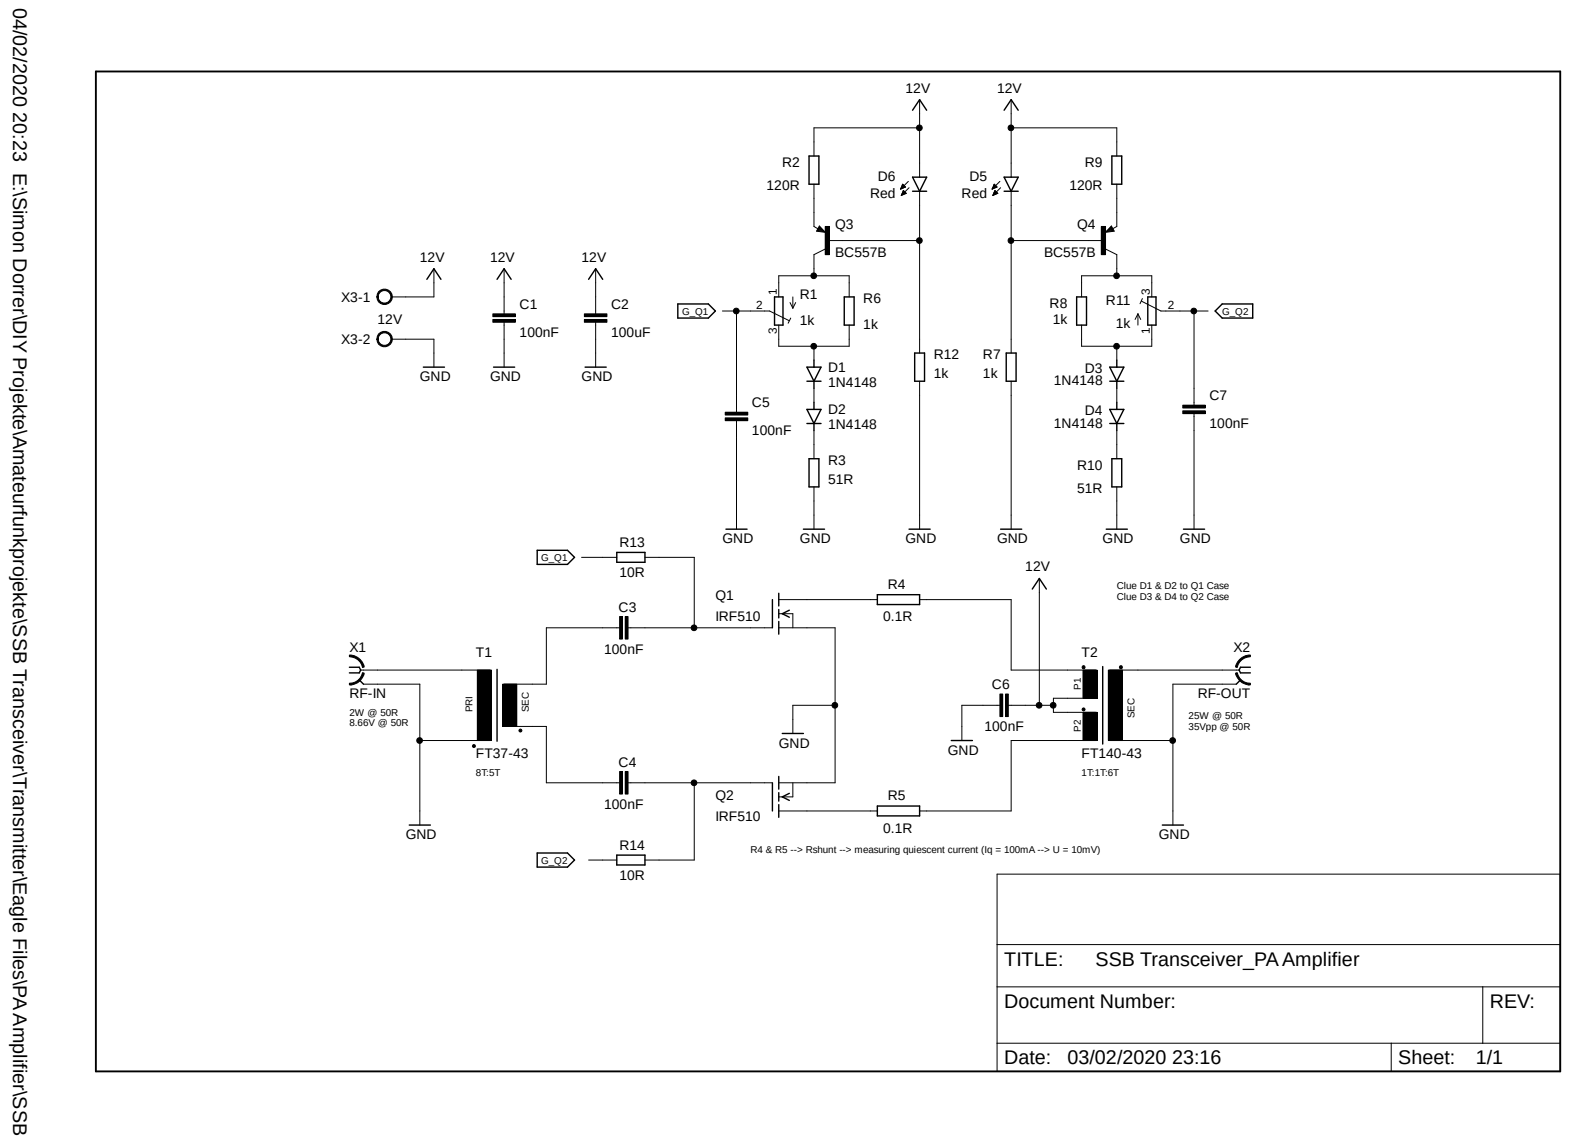
[picture p37: page 1]

04/02/2020 20:23 E:\Simon Dorrer\DIY Projekte\Amateurfunkprojekte\SSB Transceiver\Transmitter\Eagle Files\PA Amplifier\SSB Transceiver_PA Amplifier.sch (Sheet: 1/1) 2W @ 50R 8.66V @ 50R 25W @ 50R 35Vpp @ 50R Clue D1 & D2 to Q1 Case Clue D3 & D4 to Q2 Case 8T:5T 1T:1T:6T R4 & R5 --> Rshunt --> measuring quiescent current (Iq = 100mA --> U = 10mV) 12V GND100nF GND 12V IRF510 IRF510 FT37-43 RF-IN RF-OUT 12V GND 100nF 100nF GND FT140-43 100nF GND 12V BC557B BC557B 0.1R 0.1R GND 100uF 12V GND Red 100nF 100nF 120R 120R 1k 1k 1k 1k 1k 51R 51R 1N4148 1N4148 1N4148 1N4148 GND GND GND GND GND 12V 12V Red 1k GND 10R 10R C1 Q1 Q2 T1 X1 X2 C3 C4 T2 C6 Q3 Q4 R4 R5 C2 D5 C5 C7 R2 R9 R7 R6 R8

1 3 R11 2 R3 R10 D1 D2 D3 D4 X3-1 X3-2 D6 R12 R13 R14 G_Q2 G_Q2 G_Q1 G_Q1 Date: Sheet: REV: TITLE: Document Number: 03/02/2020 23:16 1/1 SSB Transceiver_PA Amplifier
