simi1505/20m-SSB-TRX-Prototype-OE3SDE/Receiver/Simulations/Crystal Ladder Filter/Crystal Ladder Filter.asc

C1: cap; 20p
C2: cap; 16.5p
C3: cap; 20p
C4: cap; 16.5p
C5: cap; 20p
C6: xtal; 5.05e-15; Rser=70 Lser=0.06189 Rpar=1e20 Cpar=5p
C7: xtal; 5.05e-15; Rser=70 Lser=0.06189 Rpar=1e20 Cpar=5p
C8: xtal; 5.05e-15; Rser=70 Lser=0.06189 Rpar=1e20 Cpar=5p
C9: xtal; 5.05e-15; Rser=70 Lser=0.06189 Rpar=1e20 Cpar=5p
R1: res; 750
R2: res; 750
V1: voltage; SINE(0 1 1); AC 1
Named nets: 0
.ac dec 1000 7000000 10000000
