simi1505/20m-SSB-TRX-Prototype-OE3SDE/Receiver/Simulations/IF Amplifier/IF Amplifier.asc

C1: cap; 100n
C2: cap; 1µ
C3: cap; 100n
C5: cap; 100n
C6: cap; 100µF
L3: ind2; 8.75µ
L4: ind2; 17.15µ
Q1: npn; MMBT3904
R1: res; 100
R2: res; 300
R3: res; 12k
R4: res; 62k
R5: res; 1.5k
R6: res; 1.5k
R8: res; 750
V1: voltage; 12
V2: voltage; SINE(0 0.1 9000000); AC 1
Named nets: 0
K1 L3 L4 1
.tran 0 0.00002 0.00001
