simi1505/20m-SSB-TRX-Prototype-OE3SDE/Receiver/Simulations/LC Double Tuned Bandpass Filters/LC Double Tuned Bandpass Filters.asc

C6: cap; 37.7p
C7: cap; 18p
C8: cap; 5.7p
C9: cap; 18p
C10: cap; 37.7p
L3: ind; 2.12µ
L4: ind; 2.12µ
R3: res; 50
R4: res; 50
V2: voltage; SINE(0 1 1); AC 1
Named nets: 0
.ac dec 1000 1000000 100000000
