simi1505/20m-SSB-TRX-Prototype-OE3SDE/Receiver/Simulations/SA612 Mixer/SA612 Mixer.asc

C1: cap; 100n
C2: cap; 1n
C3: cap; 47p
C4: cap; 100n
C5: cap; 100n
C6: cap; 1n
C7: cap; 47p
C8: cap; 100n
R1: res; 50
V1: voltage; SINE(0 500m 1000); AC 300m
V2: voltage; 5
V3: voltage; SINE(0 75m 9000000); AC 75m
V5: voltage; 5
V6: voltage; SINE(0 75m 9000000); AC 75m
X1: sa612
X3: sa612
Named nets: 0
.tran 0 0.002 0
