simi1505/20m-SSB-TRX-Prototype-OE3SDE/Receiver/Simulations/SA612 Mixer/SA612.asc

C1: cap; 2p
C2: cap; 2p
E1: e; .4
E2: e; .4
E3: e; 1
Q1: npn; MRF9411
Q2: npn; MRF9411
Q3: npn; MRF9411
Q4: npn; MRF9411
Q5: npn; MRF9411
Q6: npn; MRF9411
Q7: npn; MRF9411
Q8: npn; MRF9411
R1: res; 1500
R2: res; 1500
R5: res; 13k
R6: res; 2500
R7: res; 2500
R9: res; 210
R10: res; 18k
R11: res; 450
R12: res; 25k
R13: res; 25k
R15: res; 18k
V2: voltage; 1.32
Named nets: 5, 4, 8, 6, 7, 2, 1, 3, TP1
Bias
Osc buffer/
level shifter
*Low Noise, High-Frequency Transistor
*MOT Si 250mW  10V  50mA 8GHz 
.MODEL MRF9411 NPN 
+ IS = 4.558E-16 
+ BF = 136 
+ NF = 0.9979 
+ VAF = 21 
+ IKF = 0.7 
+ ISE = 3.087E-14 
+ NE = 2 
+ BR = 42 
+ NR = 0.993 
+ VAR = 2.9 
+ IKR = 0.016 
+ ISC = 3.411E-17 
+ NC = 1.087 
+ RB = 7 
+ IRB = 8E-05 
+ RBM = 8 
+ RE = 0.45 
+ RC = 8 
+ XTB = 0 
+ EG = 1.11 
+ XTI = 3 
+ CJE = 8.6E-13 
+ VJE = 0.94 
+ MJE = 0.42 
+ CJC = 4.3E-13 
+ VJC = 0.35 
+ MJC = 0.21 
+ XCJC = 0.44 
+ TF = 1.3E-11 
+ XTF = 400 
+ VTF = 6 
+ ITF = 1.5 
+ PTF = 47 
+ TR = 1E-09 
+ FC = 0.98
>>>MEASURED PART DC PERFORMANCE<<<
PIN     V(4v)     V(5V)     V(6v)     V(8v)
1         1.35v    1.38v     1.39v     1.42v
2         1.35v    1.38v     1.19v     1.42v
3         GND     GND      GND      GND
4         2.94v    3.90v     4.90v     6.83v 
5         2.96v    3.88v     4.88v     6.81v
6         4.03v    4.95v     5.95v     7.97v
7         3.25v    4.02v     5.02v     7.19v
8          VDD     VDD      VDD       VDD
 
Idd      2.0ma    2.2ma    2.3 ma    2.8ma
By:
Joe Rocci
W3JDR
joe@roccis.com
Up to date model files and application
circuit files can be found at:
http://w3jdr.ham-radio-op.net
>>>NE602/SA612 OSCILLATOR/MIXER IC MODEL<<<
