simi1505/20m-SSB-TRX-Prototype-OE3SDE/Transmitter/Simulations/Buffer Amplifier/Buffer Amplifier.asc

C1: cap; 100n
C2: cap; 100n
C5: cap; 100n
C6: cap; 100µF
Q1: npn; MMBT3904
R1: res; 2.7k
R2: res; 3.9k
R3: res; 165
R4: res; 180
V1: voltage; 12
V2: voltage; SINE(0 3 14.15MEG); AC 5
Named nets: 0
.tran 0 0.00002 0.00001
