simi1505/20m-SSB-TRX-Prototype-OE3SDE/Transmitter/Simulations/Driver Amplifier/Driver Amplifier.asc

C1: cap; 100n
C2: cap; 100n
C3: cap; 100n
C4: cap; 100n
C5: cap; 100n
C6: cap; 100µF
L3: ind2; 113.4µ
L4: ind2; 5.6µ
L5: ind2; 8.75µ
L6: ind2; 8.75µ
Q1: npn; MMBT3904
Q2: npn; 2SC5171
R1: res; 8.5
R2: res; 56
R3: res; 3.3k
R4: res; 15k
R5: res; 3.3
R6: res; 43
R7: res; 50
R8: res; 180
R9: res; 1k
R10: res; 220
V1: voltage; 12
V2: voltage; SINE(0 0.1 14000000); AC 1
Named nets: 0
K1 L3 L4 1
K2 L5 L6  1
.tran 0 0.000002 0.000001
