simi1505/20m-SSB-TRX-Prototype-OE3SDE/Transmitter/Simulations/LC Double Tuned Bandpass Filters/LC Double Tuned Bandpass Filters.asc

C6: cap; 3p
C7: cap; 55.3p
C8: cap; 1p
C9: cap; 50.1p
C10: cap; 8.2p
L3: ind; 2.12µ
L4: ind; 2.12µ
R3: res; 1500
R4: res; 180
V2: voltage; SINE(0 1 1); AC 1
Named nets: 0
.ac dec 1000 13000000 15000000
