simi1505/20m-SSB-TRX-Prototype-OE3SDE/Transmitter/Simulations/LC Lowpass Filter/LC Lowpass Filter.asc

C1: cap; 220pF
C2: cap; 440pF
C3: cap; 220pF
L1: ind; 680n
L2: ind; 680n
R3: res; 50
R4: res; 50
V2: voltage; SINE(0 1 1); AC 1
Named nets: 0
.ac dec 1000 10000000 50000000
