simi1505/20m-SSB-TRX-Prototype-OE3SDE/Transmitter/Simulations/Power Amplifier/Power Amplifier.asc

C1: cap; 100n
C2: cap; 100n
C3: cap; 100n
C4: cap; 100µ
C5: cap; 100n
C6: cap; 1µ
C7: cap; 1µ
D1: diode; 1N4148
D2: diode; 1N4148
D3: diode; 1N4148
D4: diode; 1N4148
D5: diode; 1N4148
D6: diode; 1N4148
D7: diode; 1N4148
D8: diode; 1N4148
D9: diode; 1N4148
D10: diode; 1N4148
L1: ind2; 0.89µ
L2: ind2; 0.89µ
L3: ind2; 31.86µ
L4: ind2; 8.75µ
L5: ind2; 22.4µ
M1: nmos; IRF510
M2: nmos; IRF510
Q1: pnp; BC557B
Q2: pnp; BC557B
R1: res; 0.1
R2: res; 0.1
R3: res; 50
R4: res; 50
R5: res; 1k
R6: res; 620
R7: res; 380
R8: res; 51
R9: res; 120
R10: res; 1k
R11: res; 10
R12: res; 10
R13: res; 1k
R14: res; 1k
R15: res; 620
R16: res; 120
R17: res; 380
R18: res; 51
V1: voltage; SINE(0 10 14000000); AC 1
V2: voltage; 12
Named nets: 0
K2 L1 L2 L3 1
K2 L4 L5 1
.tran 0 0.000002 0.000001
