simi1505/20m-SSB-TRX-Prototype-OE3SDE/Transmitter/Simulations/Supply EMI Filter/Supply EMI Filter.asc

C1: cap; 1.678pF
C2: cap; 10µ
C3: cap; 10n
C4: cap; 10n
C5: cap; 10n
C6: cap; 670p
C7: cap; 10n
C8: cap; 670p
C9: cap; 670p
C10: cap; 670p
L1: ind; 1.208µF
L2: FerriteBead; 1.208µ; Rser=0.3 Rpar=1.082k Cpar=1.678p
L3: FerriteBead; 1.208µ; Rser=0.3 Rpar=1.082k Cpar=1.678p
L4: ind; 680n
L5: ind; 680n
R1: res; 0.3
R2: res; 1.082k
R3: res; 100000
R4: res; 50
R5: res; 10
R6: res; 1k
V1: voltage; ""; AC 1
V2: voltage; ""; AC 1
V3: voltage; ""; AC 1
V4: voltage; ""; AC 1
V5: voltage; ""; AC 1
Named nets: 0
.ac dec 10 1k 10G
