simi1505/20m-SSB-TRX-Prototype-OE3SDE/Receiver/Eagle Files/Speaker Amplifier/SSB Transceiver_Speaker Amplifier.brd

## EAGLE design Receiver/Eagle Files/Speaker Amplifier/SSB Transceiver_Speaker Amplifier.brd (2025-07-19)

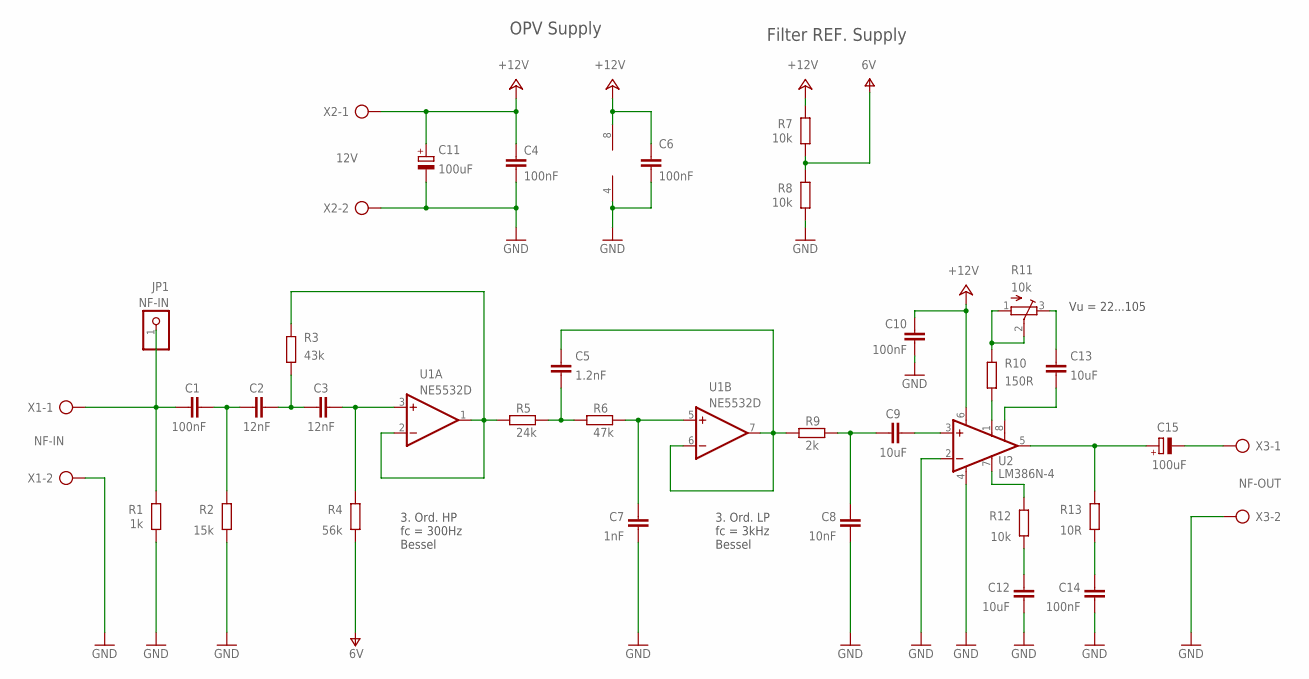
[picture p59: schematic SSB Transceiver_Speaker Amplifier.sch]

Parts:
C1, C4, C6, C10, C14: 100nF; C0805
C2, C3: 12nF; C0805
C5: 1.2nF; C0805
C7: 1nF; C0805
C8: 10nF; C0805
C9, C12, C13: 10uF; C0805
C11, C15: 100uF; E2,5-6
JP1: NF-IN; 1X01
R1: 1k; R0805
R2: 15k; R0805
R3: 43k; R0805
R4: 56k; R0805
R5: 24k; R0805
R6: 47k; R0805
R7, R8, R12: 10k; R0805
R9: 2k; R0805
R10: 150R; R0805
R11: 10k; 3223G
R13: 10R; R0805
U1: NE5532D; SO08
U2: LM386N-4; DIL08
X1: NF-IN; AK300/2
X2: 12V; AK300/2
X3: NF-OUT; AK300/2

Connections:
+24V: C4.2, C6.2, C10.2, C11.+, R7.1, U1.8 (V+), U2.6 (VS), X2.1
GND: C4.1, C6.1, C7.1, C8.1, C10.1, C11.-, C12.1, C14.1, R1.2, R2.2, R8.2, U1.4 (V-), U2.2 (-IN), U2.4 (GND), X1.2, X2.2, X3.2
unnamed: C9.2, U2.3 (+IN)
unnamed: R12.1, U2.7 (BYPASS)
unnamed: C12.2, R12.2
unnamed: C1.1, JP1.1, R1.1, X1.1
unnamed: C15.+, R13.1, U2.5 (OUT)
unnamed: C14.2, R13.2
unnamed: R10.2, U2.1 (GAIN)
unnamed: C1.2, C2.1, R2.1
unnamed: C13.2, R11.3 (E)
unnamed: C15.-, X3.1
unnamed: C13.1, U2.8 (GAIN)
unnamed: R3.1, R5.2, U1.1 (OUT), U1.2 (-IN)
unnamed: C2.2, C3.1, R3.2
unnamed: C3.2, R4.1, U1.3 (+IN)
unnamed: C5.1, R5.1, R6.2
unnamed: C7.2, R6.1, U1.5 (+IN)
unnamed: C5.2, R9.2, U1.6 (-IN), U1.7 (OUT)
unnamed: C8.2, C9.1, R9.1
unnamed: R10.1, R11.1 (A), R11.2 (S)
V+: R4.2, R7.2, R8.1

Notes on the sheet:
OPV Supply
Filter REF. Supply
3. Ord. HP fc = 300Hz Bessel
3. Ord. LP fc = 3kHz Bessel
Vu = 22...105

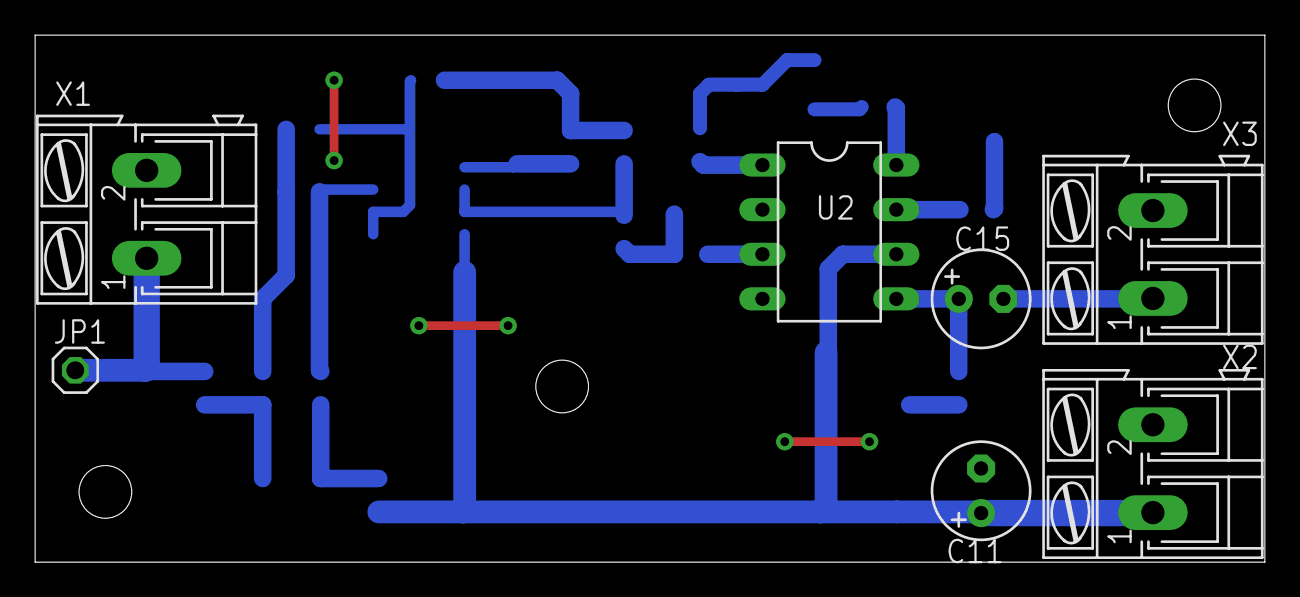
[picture p60: board SSB Transceiver_Speaker Amplifier.brd from above]

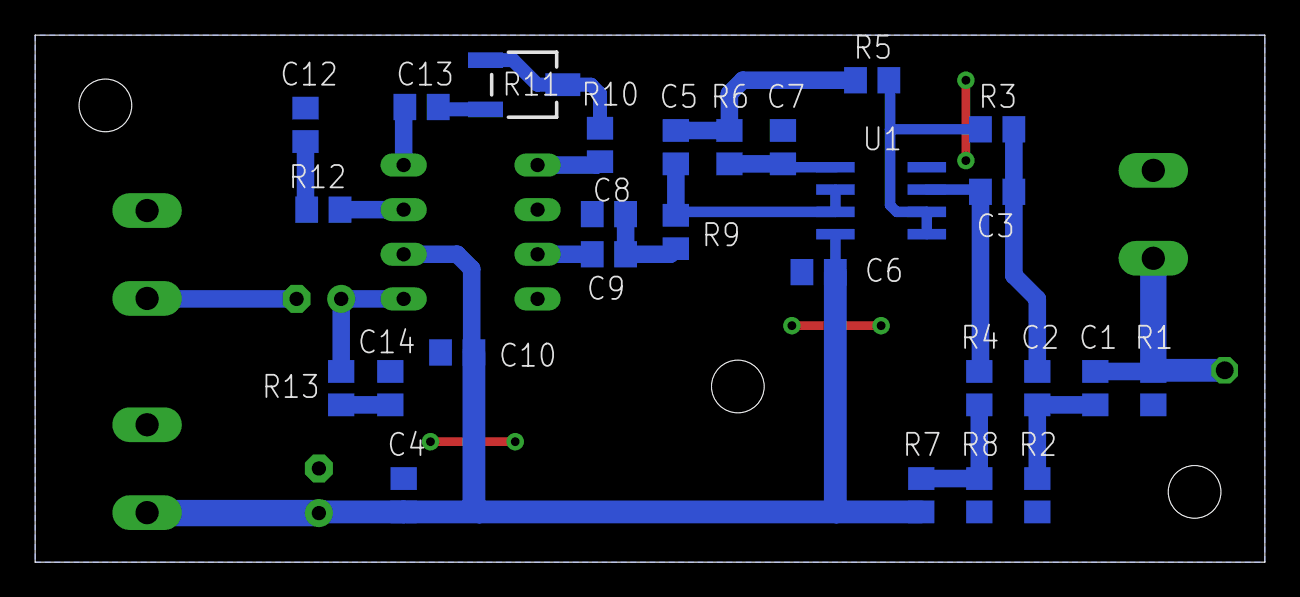
[picture p61: board SSB Transceiver_Speaker Amplifier.brd from below]

Board: 2 copper layers, 70.0 x 30.0 mm, 34 parts (27 on the bottom side), 22 nets.
