simi1505/20m-SSB-TRX-Prototype-OE3SDE/TXPWR-Switch/SSB Transceiver_TXPWR-Switch.brd

## EAGLE design TXPWR-Switch/SSB Transceiver_TXPWR-Switch.brd (2025-07-19)

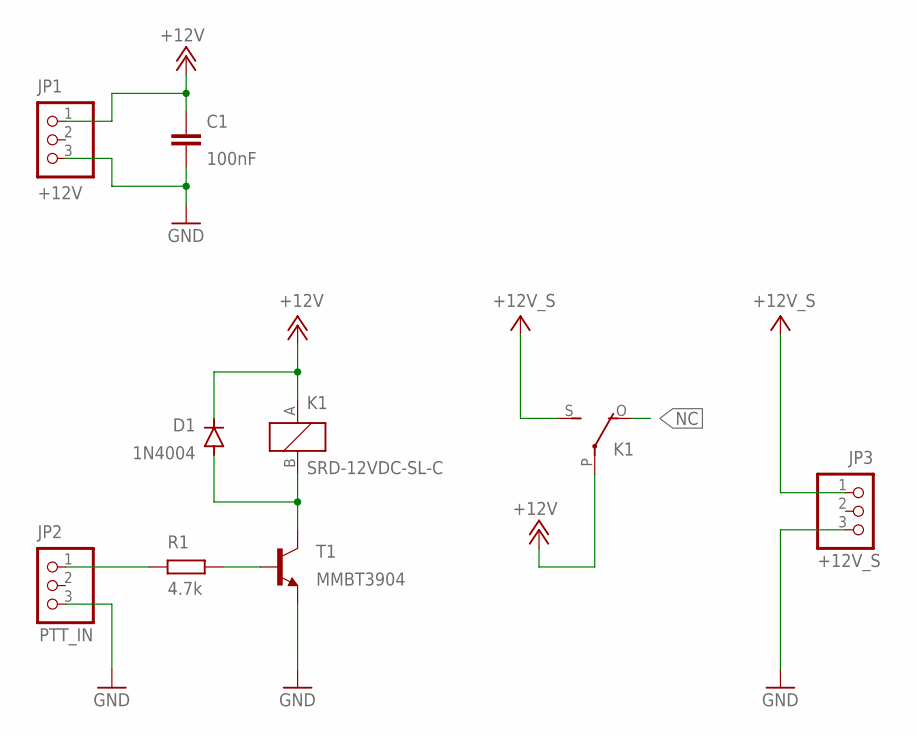
[picture p62: schematic SSB Transceiver_TXPWR-Switch.sch]

Parts:
C1: 100nF; C0805K
D1: 1N4004; DO41-10
JP1: +12V; 1X03
JP2: PTT_IN; 1X03
JP3: +12V_S; 1X03
K1: SRD-12VDC-SL-C
R1: 4.7k; R0805
T1: MMBT3904; SOT23-BEC

Connections:
+12V: C1.1, D1.C, JP1.1, K1.A, K1.P
+12V_S: JP3.1, K1.S
GND: C1.2, JP1.3, JP2.3, JP3.3, T1.E
unnamed: R1.2, T1.B
unnamed: D1.A, K1.B, T1.C
unnamed: JP2.1, R1.1
NC: K1.O

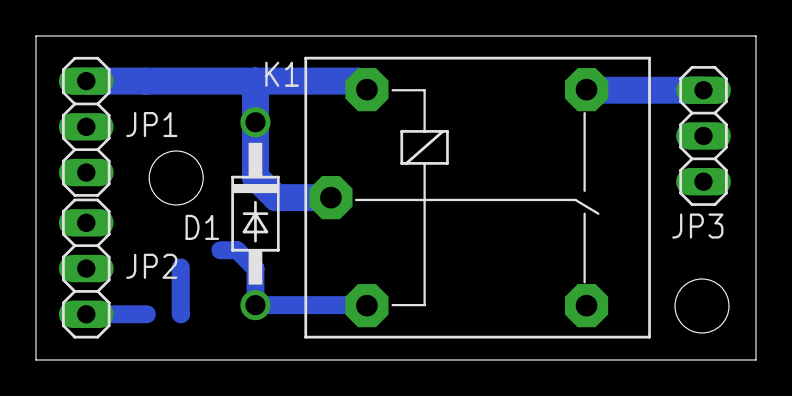
[picture p63: board SSB Transceiver_TXPWR-Switch.brd from above]

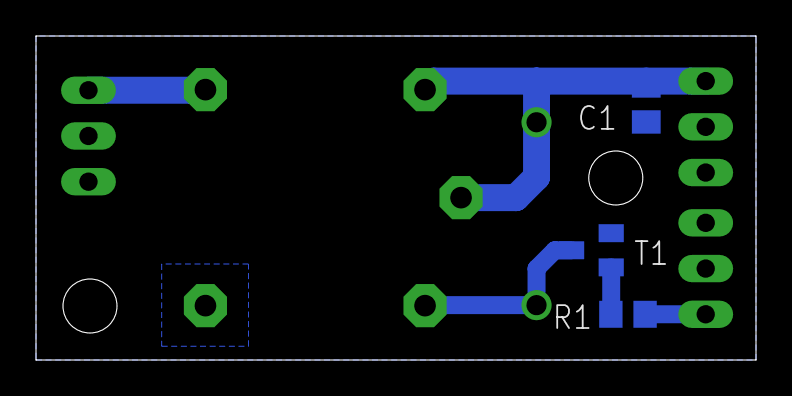
[picture p64: board SSB Transceiver_TXPWR-Switch.brd from below]

Board: 2 copper layers, 40.0 x 18.0 mm, 8 parts (3 on the bottom side), 6 nets.
