simi1505/20m-SSB-TRX-Prototype-OE3SDE/Transmitter/Eagle Files/Supply EMI Filter/SSB Transceiver_Supply EMI Filter.brd

## EAGLE design Transmitter/Eagle Files/Supply EMI Filter/SSB Transceiver_Supply EMI Filter.brd (2025-07-19)

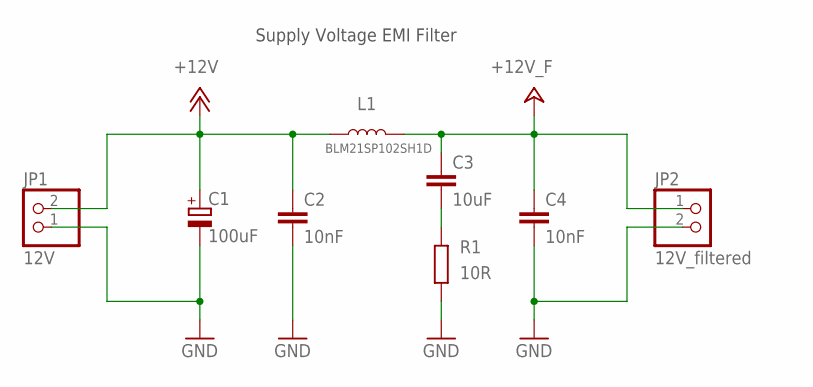
[picture p65: schematic SSB Transceiver_Supply EMI Filter.sch]

Parts:
C1: 100uF; E2,5-7
C2, C4: 10nF; C0805
C3: 10uF; C0805
JP1: 12V; 1X02
JP2: 12V_filtered; 1X02
L1: BLM21SP102SH1D; 0805
R1: 10R; R0805

Connections:
+12V: C1.+, C2.1, JP1.2, L1.1
+24V: C3.1, C4.1, JP2.1, L1.2
GND: C1.-, C2.2, C4.2, JP1.1, JP2.2, R1.1
unnamed: C3.2, R1.2

Notes on the sheet:
Supply Voltage EMI Filter

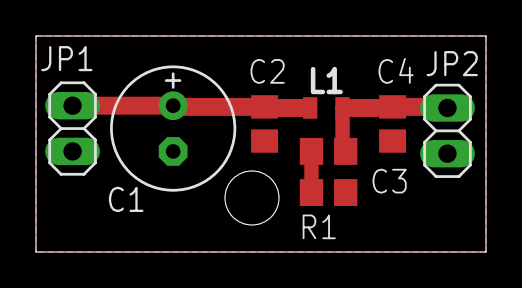
[picture p66: board SSB Transceiver_Supply EMI Filter.brd from above]

Board: 2 copper layers, 25.0 x 12.0 mm, 8 parts (0 on the bottom side), 4 nets.
