simi1505/20m-SSB-TRX-Prototype-OE3SDE/TX-RX-Switch/SSB Transceiver_TX-RX-Switch.brd

## EAGLE design TX-RX-Switch/SSB Transceiver_TX-RX-Switch.brd (2025-07-19)

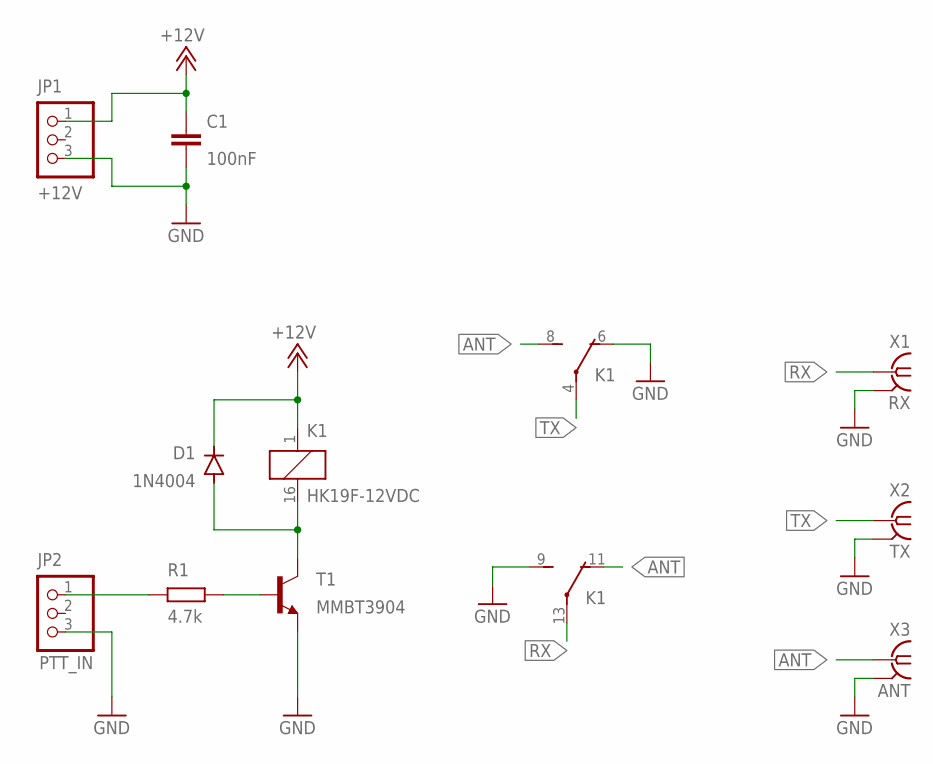
[picture p67: schematic SSB Transceiver_TX-RX-Switch.sch]

Parts:
C1: 100nF; C0805K
D1: 1N4004; DO41-10
JP1: +12V; 1X03
JP2: PTT_IN; 1X03
K1: HK19F-12VDC
R1: 4.7k; R0805
T1: MMBT3904; SOT23-BEC
X1: RX; J502-ND-142-0711-821/826_BOTTOM
X2: TX; J502-ND-142-0711-821/826_BOTTOM
X3: ANT; J502-ND-142-0711-821/826_BOTTOM

Connections:
+12V: C1.1, D1.C, JP1.1, K1.1 (A)
ANT: K1.8 (S), K1.11 (O), X3.RF
GND: C1.2, JP1.3, JP2.3, K1.6 (O), K1.9 (S), T1.E, X1.G@1 (GND), X1.G@2 (GND), X2.G@1 (GND), X2.G@2 (GND), X3.G@1 (GND), X3.G@2 (GND)
unnamed: R1.2, T1.B
unnamed: D1.A, K1.16 (B), T1.C
unnamed: JP2.1, R1.1
RX: K1.13, X1.RF
TX: K1.4, X2.RF

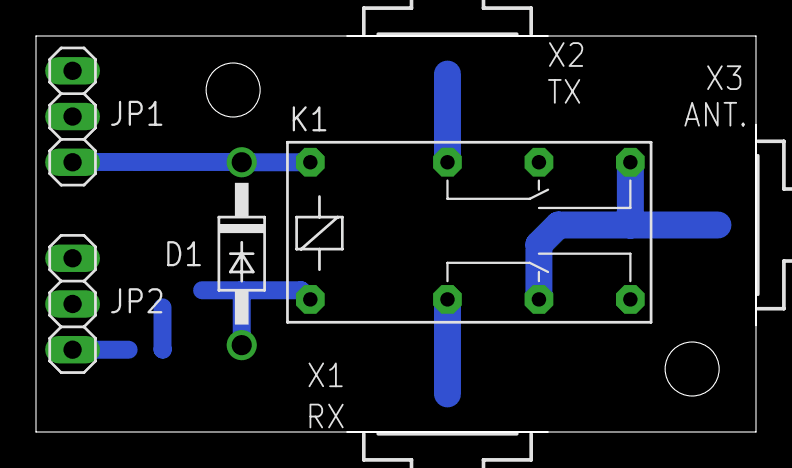
[picture p68: board SSB Transceiver_TX-RX-Switch.brd from above]

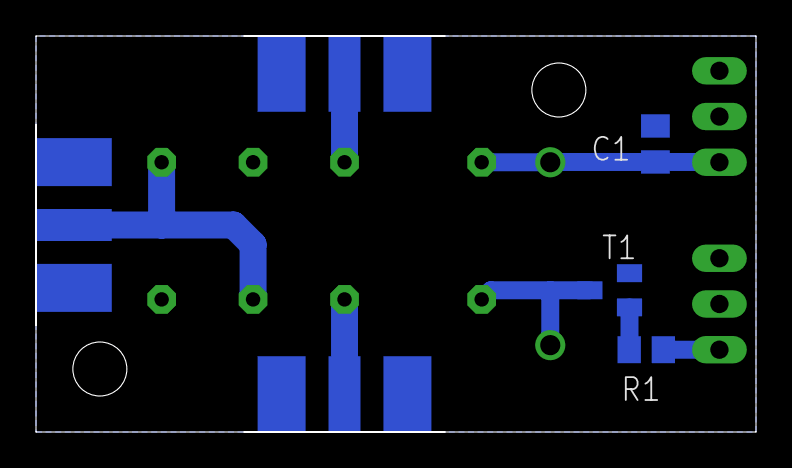
[picture p69: board SSB Transceiver_TX-RX-Switch.brd from below]

Board: 2 copper layers, 40.0 x 22.0 mm, 10 parts (3 on the bottom side), 8 nets.
