simi1505/20m-SSB-TRX-Prototype-OE3SDE/Transmitter/Eagle Files/Power Amplifier/SSB Transceiver_Power Amplifier.brd

## EAGLE design Transmitter/Eagle Files/Power Amplifier/SSB Transceiver_Power Amplifier.brd (2025-07-19)

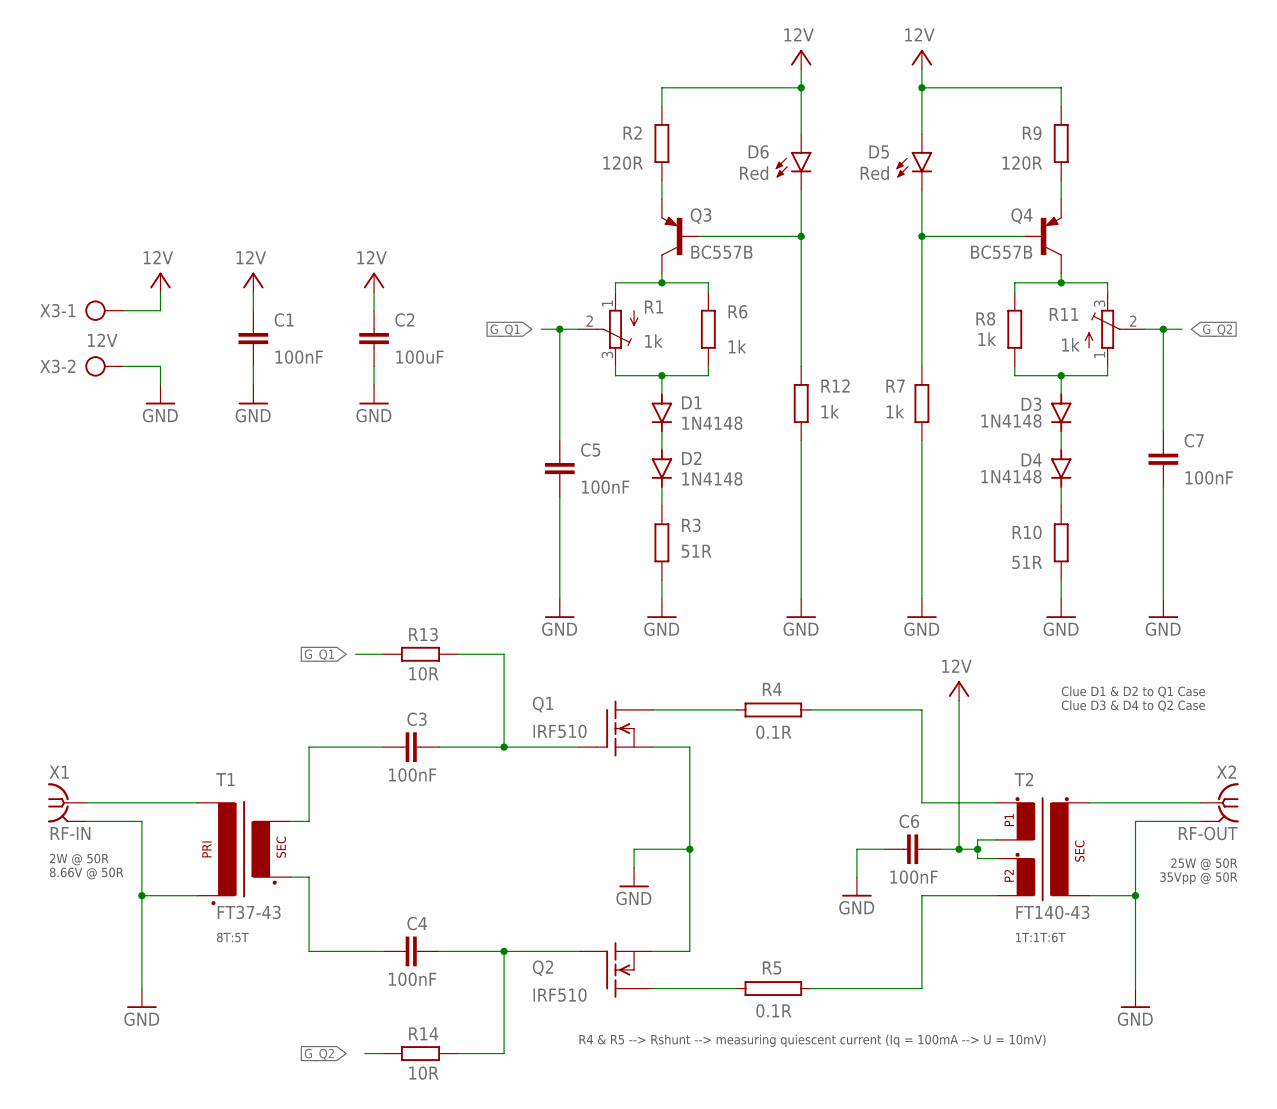
[picture p70: schematic SSB Transceiver_Power Amplifier.sch]

Parts:
C1, C3, C4, C5, C6, C7: 100nF; C0805
C2: 100uF; C0805
D1, D2, D3, D4: 1N4148; SOD323-W
D5, D6: Red; CHIP-LED0805
Q1, Q2: IRF510; TO220
Q3, Q4: BC557B; TO92-EBC
R1, R11: 1k; 3223G
R2, R9: 120R; R0805
R3, R10: 51R; R0805
R4, R5: 0.1R; MNS-5
R6, R7, R8, R12: 1k; R0805
R13, R14: 10R; R0805
T1: FT37-43; FT37-43SMD
T2: FT140-43; FT37-43CENTERTAPSMD
X1: RF-IN; J502-ND-142-0711-821/826
X2: RF-OUT; J502-ND-142-0711-821/826
X3: 12V; AK300/2

Connections:
GND: C1.1, C2.1, C5.1, C6.1, C7.1, Q1.3 (S), Q2.3 (S), R3.1, R7.1, R10.1, R12.1, T1.P$2 (P2), T2.S$2 (S2), X1.G@1 (2), X1.G@2 (2), X1.G@3 (2), X1.G@4 (2), X2.G@1 (2), X2.G@2 (2), X2.G@3 (2), X2.G@4 (2), X3.2
G_Q1: C5.2, R1.2 (S), R13.2
G_Q2: C7.2, R11.2 (S), R14.2
unnamed: C3.2, T1.S$1 (S1)
unnamed: C4.2, T1.S$2 (S2)
unnamed: T1.P$1 (P1), X1.1
unnamed: Q4.C, R8.2, R11.3 (E)
unnamed: Q3.E, R2.1
unnamed: R4.1, T2.P$1 (P1_1)
unnamed: D3.A, R8.1, R11.1 (A)
unnamed: R5.2, T2.P$4 (P2_2)
unnamed: Q1.2 (D), R4.2
unnamed: T2.S$1 (S1), X2.1
unnamed: Q2.2 (D), R5.1
unnamed: D5.C, Q4.B, R7.2
unnamed: D3.C, D4.A
unnamed: Q4.E, R9.1
unnamed: Q3.C, R1.1 (A), R6.2
unnamed: D1.C, D2.A
unnamed: D1.A, R1.3 (E), R6.1
unnamed: D2.C, R3.2
unnamed: D4.C, R10.2
unnamed: D6.C, Q3.B, R12.2
unnamed: C3.1, Q1.1 (G), R13.1
unnamed: C4.1, Q2.1 (G), R14.1
VCC: C1.2, C2.2, C6.2, D5.A, D6.A, R2.2, R9.2, T2.P$2 (P1_2), T2.P$3 (P2_1), X3.1

Notes on the sheet:
2W @ 50R 8.66V @ 50R
25W @ 50R 35Vpp @ 50R
Clue D1 & D2 to Q1 Case Clue D3 & D4 to Q2 Case
1T:1T:6T
8T:5T
R4 & R5 --> Rshunt --> measuring quiescent current (Iq = 100mA --> U = 10mV)

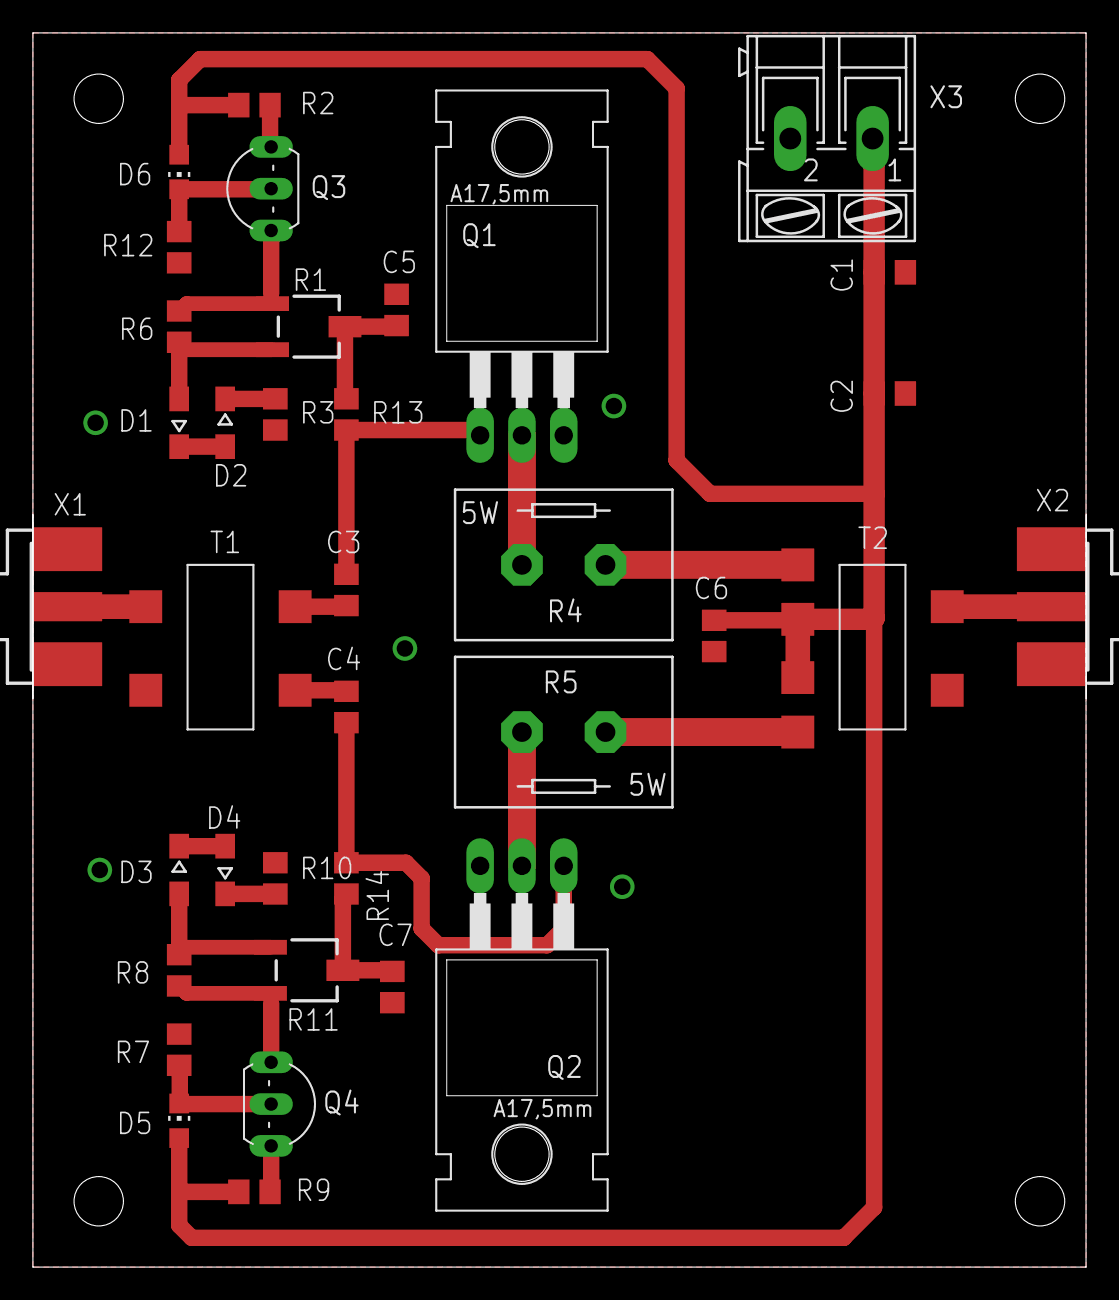
[picture p71: board SSB Transceiver_Power Amplifier.brd from above]

Board: 2 copper layers, 64.0 x 75.0 mm, 36 parts (0 on the bottom side), 26 nets.
