simi1505/20m-SSB-TRX-Prototype-OE3SDE/Supply PCB/SSB Transceiver_Supply PCB.brd

## EAGLE design Supply PCB/SSB Transceiver_Supply PCB.brd (2025-07-19)

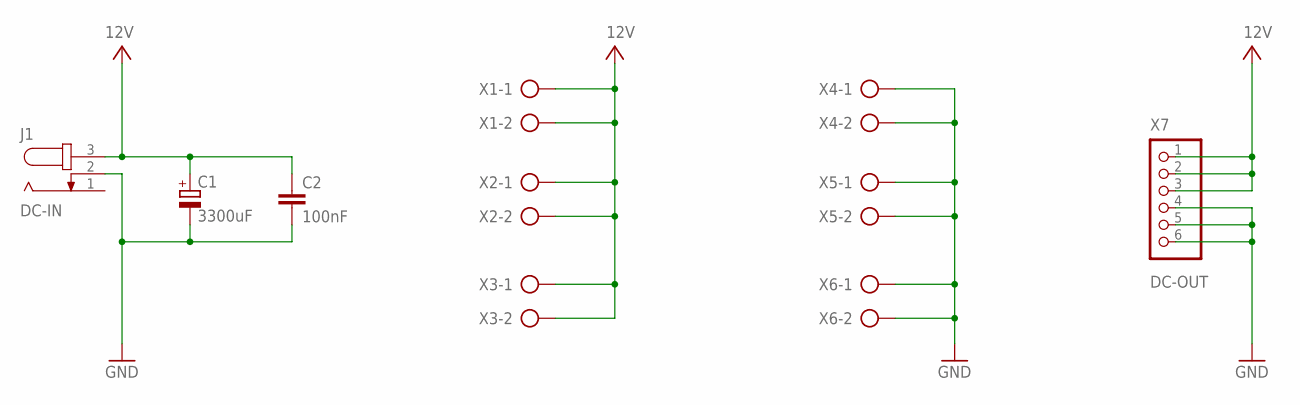
[picture p72: schematic SSB Transceiver_Supply PCB.sch]

Parts:
C1: 3300uF; E7,5-16
C2: 100nF; C0805K
J1: DC-IN; SPC4078
X1: 12V; AK300/2
X2, X3, X4, X5, X6: AK300/2
X7: DC-OUT; 1X06

Connections:
GND: C1.-, C2.2, J1.2, X4.1, X4.2, X5.1, X5.2, X6.1, X6.2, X7.4, X7.5, X7.6
VCC: C1.+, C2.1, J1.3, X1.1, X1.2, X2.1, X2.2, X3.1, X3.2, X7.1, X7.2, X7.3

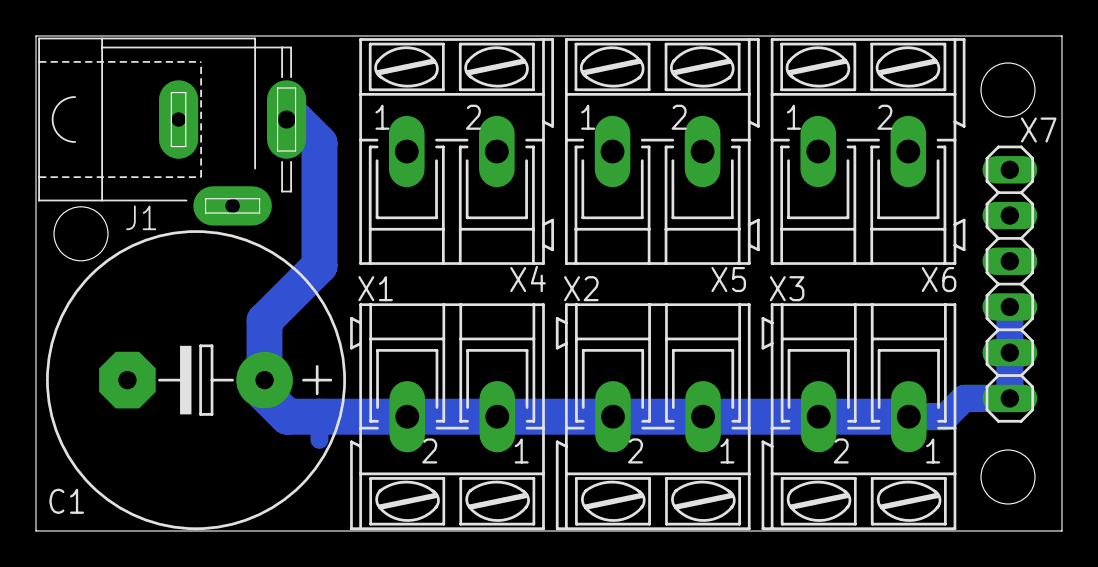
[picture p73: board SSB Transceiver_Supply PCB.brd from above]

Board: 2 copper layers, 57.0 x 27.5 mm, 10 parts (1 on the bottom side), 2 nets.
