simi1505/20m-SSB-TRX-Prototype-OE3SDE/Transmitter/Eagle Files/Driver Amplifier/SSB Transceiver_Driver Amplifier.brd

## EAGLE design Transmitter/Eagle Files/Driver Amplifier/SSB Transceiver_Driver Amplifier.brd (2025-07-19)

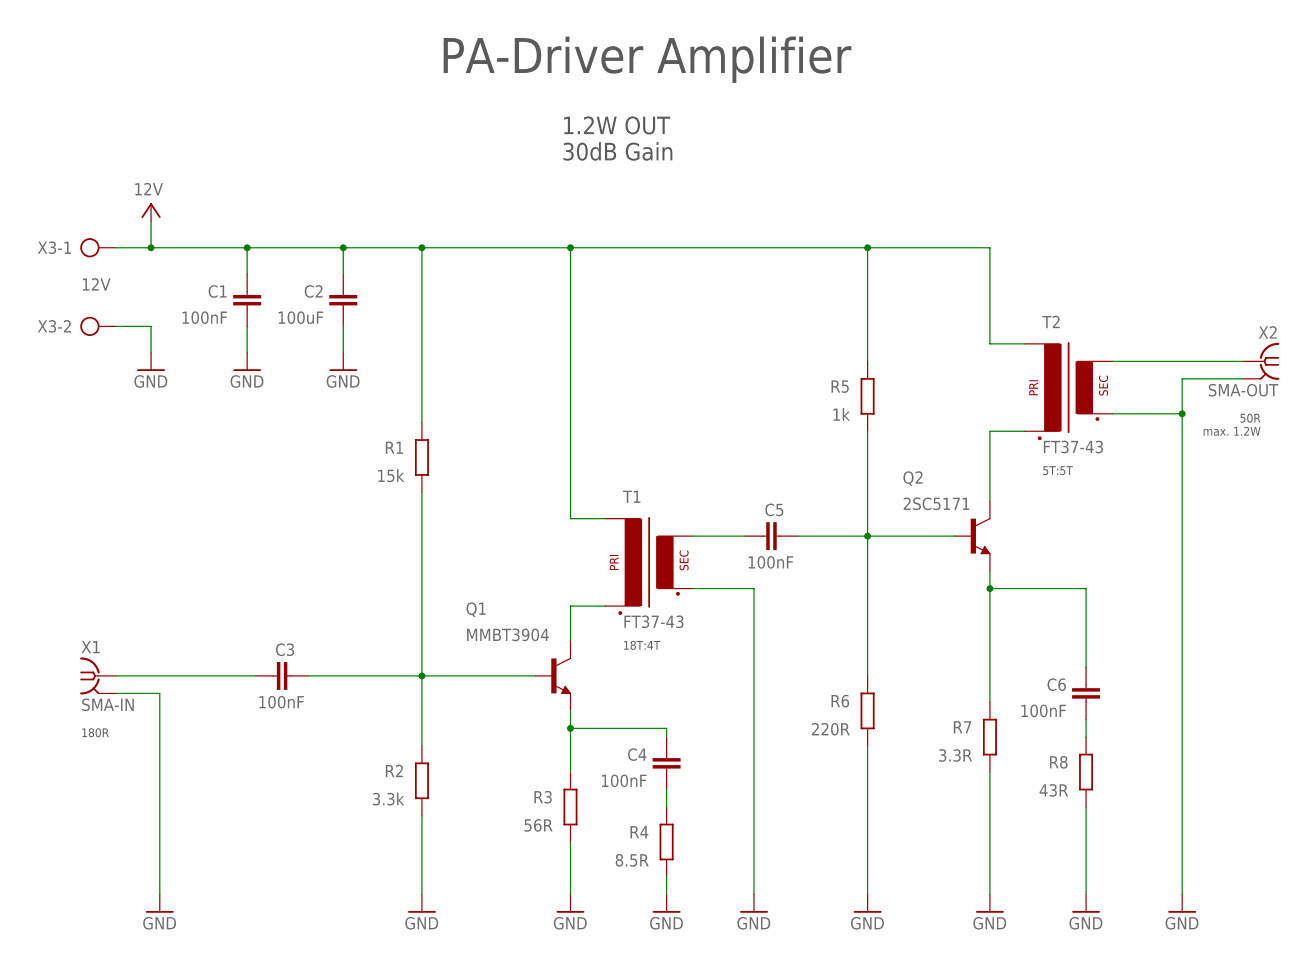
[picture p74: schematic SSB Transceiver_Driver Amplifier.sch]

Parts:
C1, C3, C4, C5, C6: 100nF; C0805
C2: 100uF; C0805
Q1: MMBT3904; SOT23-BEC
Q2: 2SC5171; TO220
R1: 15k; R0805
R2: 3.3k; R0805
R3: 56R; R0805
R4: 8.5R; R0805
R5: 1k; R0805
R6: 220R; R0805
R7: 3.3R; R0805
R8: 43R; R0805
T1, T2: FT37-43; FT37-43SMD
X1: SMA-IN; J502-ND-142-0711-821/826
X2: SMA-OUT; J502-ND-142-0711-821/826
X3: 12V; AK300/2

Connections:
GND: C1.1, C2.1, R2.2, R3.1, R4.1, R6.1, R7.1, R8.1, T1.S$2 (S2), T2.S$2 (S2), X1.G@1 (2), X1.G@2 (2), X1.G@3 (2), X1.G@4 (2), X2.G@1 (2), X2.G@2 (2), X2.G@3 (2), X2.G@4 (2), X3.2
unnamed: Q1.C, T1.P$2 (P2)
unnamed: T2.S$1 (S1), X2.1
unnamed: Q2.2 (C), T2.P$2 (P2)
unnamed: C4.2, Q1.E, R3.2
unnamed: C4.1, R4.2
unnamed: C3.1, Q1.B, R1.2, R2.1
unnamed: C3.2, X1.1
unnamed: C5.1, Q2.1 (B), R5.1, R6.2
unnamed: C6.2, Q2.3 (E), R7.2
unnamed: C5.2, T1.S$1 (S1)
unnamed: C6.1, R8.2
VCC: C1.2, C2.2, R1.1, R5.2, T1.P$1 (P1), T2.P$1 (P1), X3.1

Notes on the sheet:
50R max. 1.2W
180R
PA-Driver Amplifier
1.2W OUT 30dB Gain
5T:5T
18T:4T

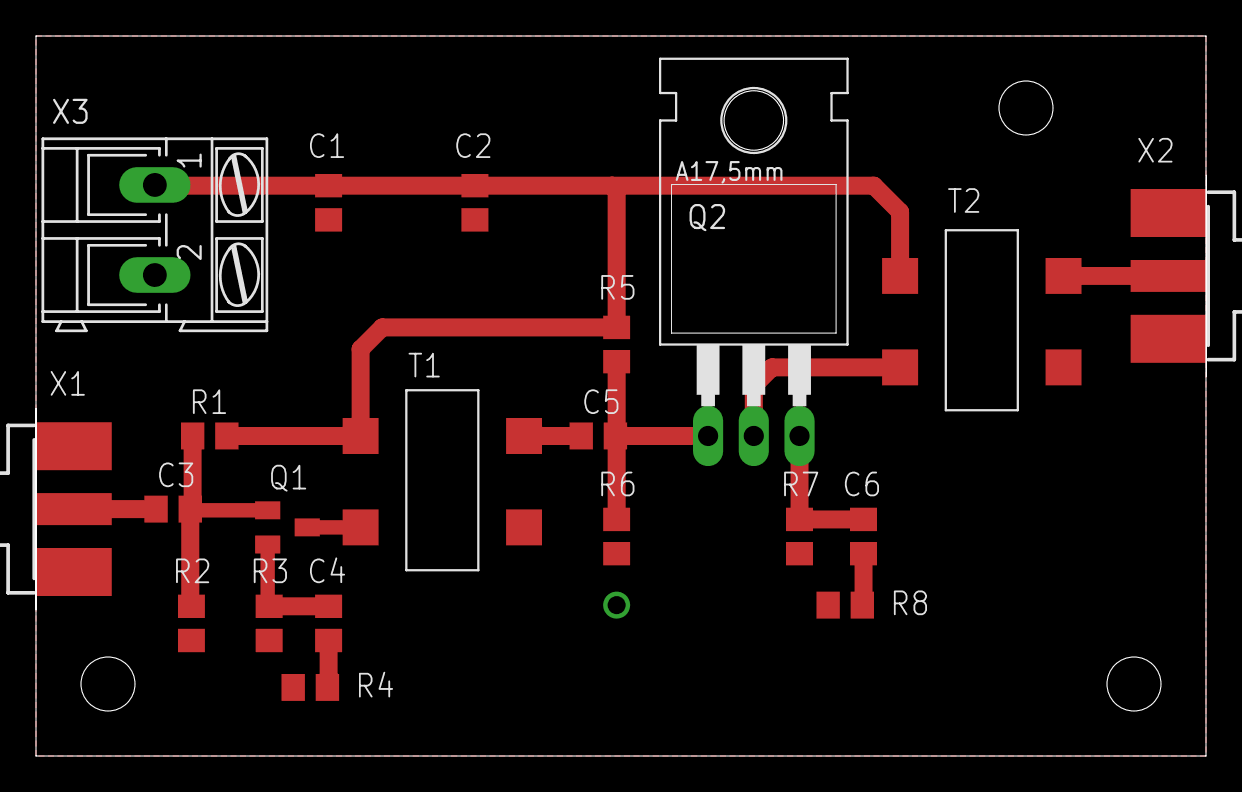
[picture p75: board SSB Transceiver_Driver Amplifier.brd from above]

Board: 2 copper layers, 65.0 x 40.0 mm, 21 parts (0 on the bottom side), 13 nets.
